MelkhiorVintageComputing/SBusFPGA/sbus-to-ztex-gateware-migen/VexRiscv_FbAccel.v

// Generator : SpinalHDL v1.7.0a    git head : 150a9b9067020722818dfb17df4a23ac712a7af8
// Component : VexRiscv
// Git hash  : 8ab9a9b12e5d8881e3a895b31b6a57d076192df0

`timescale 1ns/1ps

module VexRiscv (
  output reg          iBusWishbone_CYC,
  output reg          iBusWishbone_STB,
  input               iBusWishbone_ACK,
  output              iBusWishbone_WE,
  output     [29:0]   iBusWishbone_ADR,
  input      [31:0]   iBusWishbone_DAT_MISO,
  output     [31:0]   iBusWishbone_DAT_MOSI,
  output     [3:0]    iBusWishbone_SEL,
  input               iBusWishbone_ERR,
  output     [2:0]    iBusWishbone_CTI,
  output     [1:0]    iBusWishbone_BTE,
  output              dBusWishbone_CYC,
  output              dBusWishbone_STB,
  input               dBusWishbone_ACK,
  output              dBusWishbone_WE,
  output     [27:0]   dBusWishbone_ADR,
  input      [127:0]  dBusWishbone_DAT_MISO,
  output     [127:0]  dBusWishbone_DAT_MOSI,
  output     [15:0]   dBusWishbone_SEL,
  input               dBusWishbone_ERR,
  output     [2:0]    dBusWishbone_CTI,
  output     [1:0]    dBusWishbone_BTE,
  input               clk,
  input               reset
);
  localparam ShiftCtrlEnum_DISABLE_1 = 2'd0;
  localparam ShiftCtrlEnum_SLL_1 = 2'd1;
  localparam ShiftCtrlEnum_SRL_1 = 2'd2;
  localparam ShiftCtrlEnum_SRA_1 = 2'd3;
  localparam BranchCtrlEnum_INC = 2'd0;
  localparam BranchCtrlEnum_B = 2'd1;
  localparam BranchCtrlEnum_JAL = 2'd2;
  localparam BranchCtrlEnum_JALR = 2'd3;
  localparam CG6CtrlternaryEnum_CTRL_CMIX = 2'd0;
  localparam CG6CtrlternaryEnum_CTRL_CMOV = 2'd1;
  localparam CG6CtrlternaryEnum_CTRL_FSR = 2'd2;
  localparam CG6CtrlsignextendEnum_CTRL_SEXTdotB = 1'd0;
  localparam CG6CtrlsignextendEnum_CTRL_ZEXTdotH = 1'd1;
  localparam CG6CtrlminmaxEnum_CTRL_MAXU = 1'd0;
  localparam CG6CtrlminmaxEnum_CTRL_MINU = 1'd1;
  localparam CG6CtrlEnum_CTRL_SH2ADD = 3'd0;
  localparam CG6CtrlEnum_CTRL_minmax = 3'd1;
  localparam CG6CtrlEnum_CTRL_signextend = 3'd2;
  localparam CG6CtrlEnum_CTRL_ternary = 3'd3;
  localparam CG6CtrlEnum_CTRL_REV8 = 3'd4;
  localparam AluBitwiseCtrlEnum_XOR_1 = 2'd0;
  localparam AluBitwiseCtrlEnum_OR_1 = 2'd1;
  localparam AluBitwiseCtrlEnum_AND_1 = 2'd2;
  localparam Src3CtrlEnum_RS = 1'd0;
  localparam Src3CtrlEnum_IMI = 1'd1;
  localparam Src2CtrlEnum_RS = 2'd0;
  localparam Src2CtrlEnum_IMI = 2'd1;
  localparam Src2CtrlEnum_IMS = 2'd2;
  localparam Src2CtrlEnum_PC = 2'd3;
  localparam AluCtrlEnum_ADD_SUB = 2'd0;
  localparam AluCtrlEnum_SLT_SLTU = 2'd1;
  localparam AluCtrlEnum_BITWISE = 2'd2;
  localparam Src1CtrlEnum_RS = 2'd0;
  localparam Src1CtrlEnum_IMU = 2'd1;
  localparam Src1CtrlEnum_PC_INCREMENT = 2'd2;
  localparam Src1CtrlEnum_URS1 = 2'd3;

  wire                IBusCachedPlugin_cache_io_flush;
  wire                IBusCachedPlugin_cache_io_cpu_prefetch_isValid;
  wire                IBusCachedPlugin_cache_io_cpu_fetch_isValid;
  wire                IBusCachedPlugin_cache_io_cpu_fetch_isStuck;
  wire                IBusCachedPlugin_cache_io_cpu_fetch_isRemoved;
  wire                IBusCachedPlugin_cache_io_cpu_decode_isValid;
  wire                IBusCachedPlugin_cache_io_cpu_decode_isStuck;
  reg                 IBusCachedPlugin_cache_io_cpu_fill_valid;
  wire                dataCache_1_io_cpu_execute_isValid;
  wire       [31:0]   dataCache_1_io_cpu_execute_address;
  wire       [2:0]    dataCache_1_io_cpu_execute_args_size;
  wire                dataCache_1_io_cpu_memory_isValid;
  wire       [31:0]   dataCache_1_io_cpu_memory_address;
  reg                 dataCache_1_io_cpu_memory_mmuRsp_isIoAccess;
  reg                 dataCache_1_io_cpu_writeBack_isValid;
  reg        [127:0]  dataCache_1_io_cpu_writeBack_storeData;
  wire       [31:0]   dataCache_1_io_cpu_writeBack_address;
  wire                dataCache_1_io_cpu_writeBack_fence_SW;
  wire                dataCache_1_io_cpu_writeBack_fence_SR;
  wire                dataCache_1_io_cpu_writeBack_fence_SO;
  wire                dataCache_1_io_cpu_writeBack_fence_SI;
  wire                dataCache_1_io_cpu_writeBack_fence_PW;
  wire                dataCache_1_io_cpu_writeBack_fence_PR;
  wire                dataCache_1_io_cpu_writeBack_fence_PO;
  wire                dataCache_1_io_cpu_writeBack_fence_PI;
  wire       [3:0]    dataCache_1_io_cpu_writeBack_fence_FM;
  wire                dataCache_1_io_cpu_flush_valid;
  wire                dataCache_1_io_mem_cmd_ready;
  reg        [31:0]   _zz_RegFilePlugin_regFile_port0;
  reg        [31:0]   _zz_RegFilePlugin_regFile_port1;
  reg        [31:0]   _zz_RegFilePlugin_regFile_port2;
  wire                IBusCachedPlugin_cache_io_cpu_prefetch_haltIt;
  wire       [31:0]   IBusCachedPlugin_cache_io_cpu_fetch_data;
  wire       [31:0]   IBusCachedPlugin_cache_io_cpu_fetch_physicalAddress;
  wire                IBusCachedPlugin_cache_io_cpu_decode_error;
  wire                IBusCachedPlugin_cache_io_cpu_decode_mmuRefilling;
  wire                IBusCachedPlugin_cache_io_cpu_decode_mmuException;
  wire       [31:0]   IBusCachedPlugin_cache_io_cpu_decode_data;
  wire                IBusCachedPlugin_cache_io_cpu_decode_cacheMiss;
  wire       [31:0]   IBusCachedPlugin_cache_io_cpu_decode_physicalAddress;
  wire                IBusCachedPlugin_cache_io_mem_cmd_valid;
  wire       [31:0]   IBusCachedPlugin_cache_io_mem_cmd_payload_address;
  wire       [2:0]    IBusCachedPlugin_cache_io_mem_cmd_payload_size;
  wire                dataCache_1_io_cpu_execute_haltIt;
  wire                dataCache_1_io_cpu_execute_refilling;
  wire                dataCache_1_io_cpu_memory_isWrite;
  wire                dataCache_1_io_cpu_writeBack_haltIt;
  wire       [127:0]  dataCache_1_io_cpu_writeBack_data;
  wire                dataCache_1_io_cpu_writeBack_mmuException;
  wire                dataCache_1_io_cpu_writeBack_unalignedAccess;
  wire                dataCache_1_io_cpu_writeBack_accessError;
  wire                dataCache_1_io_cpu_writeBack_isWrite;
  wire                dataCache_1_io_cpu_writeBack_keepMemRspData;
  wire                dataCache_1_io_cpu_writeBack_exclusiveOk;
  wire                dataCache_1_io_cpu_flush_ready;
  wire                dataCache_1_io_cpu_redo;
  wire                dataCache_1_io_mem_cmd_valid;
  wire                dataCache_1_io_mem_cmd_payload_wr;
  wire                dataCache_1_io_mem_cmd_payload_uncached;
  wire       [31:0]   dataCache_1_io_mem_cmd_payload_address;
  wire       [127:0]  dataCache_1_io_mem_cmd_payload_data;
  wire       [15:0]   dataCache_1_io_mem_cmd_payload_mask;
  wire       [2:0]    dataCache_1_io_mem_cmd_payload_size;
  wire                dataCache_1_io_mem_cmd_payload_last;
  wire       [31:0]   _zz_execute_SHIFT_RIGHT;
  wire       [32:0]   _zz_execute_SHIFT_RIGHT_1;
  wire       [32:0]   _zz_execute_SHIFT_RIGHT_2;
  wire       [2:0]    _zz__zz_IBusCachedPlugin_jump_pcLoad_payload_1;
  reg        [31:0]   _zz_IBusCachedPlugin_jump_pcLoad_payload_4;
  wire       [1:0]    _zz_IBusCachedPlugin_jump_pcLoad_payload_5;
  wire       [31:0]   _zz_IBusCachedPlugin_fetchPc_pc;
  wire       [2:0]    _zz_IBusCachedPlugin_fetchPc_pc_1;
  wire       [11:0]   _zz__zz_IBusCachedPlugin_decodePrediction_cmd_hadBranch;
  wire       [31:0]   _zz_IBusCachedPlugin_decodePrediction_cmd_hadBranch_2;
  wire       [19:0]   _zz__zz_2;
  wire       [11:0]   _zz__zz_4;
  wire       [31:0]   _zz__zz_6;
  wire       [31:0]   _zz__zz_6_1;
  wire       [19:0]   _zz__zz_IBusCachedPlugin_predictionJumpInterface_payload;
  wire       [11:0]   _zz__zz_IBusCachedPlugin_predictionJumpInterface_payload_2;
  wire                _zz_IBusCachedPlugin_predictionJumpInterface_payload_4;
  wire                _zz_IBusCachedPlugin_predictionJumpInterface_payload_5;
  wire                _zz_IBusCachedPlugin_predictionJumpInterface_payload_6;
  reg        [7:0]    _zz_writeBack_DBusCachedPlugin_rspShifted;
  wire       [3:0]    _zz_writeBack_DBusCachedPlugin_rspShifted_1;
  reg        [7:0]    _zz_writeBack_DBusCachedPlugin_rspShifted_2;
  wire       [2:0]    _zz_writeBack_DBusCachedPlugin_rspShifted_3;
  reg        [7:0]    _zz_writeBack_DBusCachedPlugin_rspShifted_4;
  wire       [1:0]    _zz_writeBack_DBusCachedPlugin_rspShifted_5;
  reg        [7:0]    _zz_writeBack_DBusCachedPlugin_rspShifted_6;
  wire       [1:0]    _zz_writeBack_DBusCachedPlugin_rspShifted_7;
  reg        [7:0]    _zz_writeBack_DBusCachedPlugin_rspShifted_8;
  wire       [0:0]    _zz_writeBack_DBusCachedPlugin_rspShifted_9;
  reg        [7:0]    _zz_writeBack_DBusCachedPlugin_rspShifted_10;
  wire       [0:0]    _zz_writeBack_DBusCachedPlugin_rspShifted_11;
  reg        [7:0]    _zz_writeBack_DBusCachedPlugin_rspShifted_12;
  wire       [0:0]    _zz_writeBack_DBusCachedPlugin_rspShifted_13;
  reg        [7:0]    _zz_writeBack_DBusCachedPlugin_rspShifted_14;
  wire       [0:0]    _zz_writeBack_DBusCachedPlugin_rspShifted_15;
  wire       [31:0]   _zz__zz_decode_REGFILE_WRITE_VALID_ODD;
  wire       [31:0]   _zz__zz_decode_REGFILE_WRITE_VALID_ODD_1;
  wire       [31:0]   _zz__zz_decode_REGFILE_WRITE_VALID_ODD_2;
  wire       [31:0]   _zz__zz_decode_REGFILE_WRITE_VALID_ODD_3;
  wire                _zz__zz_decode_REGFILE_WRITE_VALID_ODD_4;
  wire       [0:0]    _zz__zz_decode_REGFILE_WRITE_VALID_ODD_5;
  wire                _zz__zz_decode_REGFILE_WRITE_VALID_ODD_6;
  wire       [0:0]    _zz__zz_decode_REGFILE_WRITE_VALID_ODD_7;
  wire       [31:0]   _zz__zz_decode_REGFILE_WRITE_VALID_ODD_8;
  wire       [28:0]   _zz__zz_decode_REGFILE_WRITE_VALID_ODD_9;
  wire       [31:0]   _zz__zz_decode_REGFILE_WRITE_VALID_ODD_10;
  wire       [31:0]   _zz__zz_decode_REGFILE_WRITE_VALID_ODD_11;
  wire                _zz__zz_decode_REGFILE_WRITE_VALID_ODD_12;
  wire       [2:0]    _zz__zz_decode_REGFILE_WRITE_VALID_ODD_13;
  wire       [31:0]   _zz__zz_decode_REGFILE_WRITE_VALID_ODD_14;
  wire       [31:0]   _zz__zz_decode_REGFILE_WRITE_VALID_ODD_15;
  wire       [31:0]   _zz__zz_decode_REGFILE_WRITE_VALID_ODD_16;
  wire       [31:0]   _zz__zz_decode_REGFILE_WRITE_VALID_ODD_17;
  wire                _zz__zz_decode_REGFILE_WRITE_VALID_ODD_18;
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
  wire       [8:0]    _zz__zz_decode_REGFILE_WRITE_VALID_ODD_84;
  wire       [1:0]    _zz__zz_decode_REGFILE_WRITE_VALID_ODD_85;
  wire       [31:0]   _zz__zz_decode_REGFILE_WRITE_VALID_ODD_86;
  wire       [31:0]   _zz__zz_decode_REGFILE_WRITE_VALID_ODD_87;
  wire                _zz__zz_decode_REGFILE_WRITE_VALID_ODD_88;
  wire       [31:0]   _zz__zz_decode_REGFILE_WRITE_VALID_ODD_89;
  wire       [31:0]   _zz__zz_decode_REGFILE_WRITE_VALID_ODD_90;
  wire       [0:0]    _zz__zz_decode_REGFILE_WRITE_VALID_ODD_91;
  wire                _zz__zz_decode_REGFILE_WRITE_VALID_ODD_92;
  wire       [5:0]    _zz__zz_decode_REGFILE_WRITE_VALID_ODD_93;
  wire       [1:0]    _zz__zz_decode_REGFILE_WRITE_VALID_ODD_94;
  wire       [31:0]   _zz__zz_decode_REGFILE_WRITE_VALID_ODD_95;
  wire                _zz__zz_decode_REGFILE_WRITE_VALID_ODD_96;
  wire       [31:0]   _zz__zz_decode_REGFILE_WRITE_VALID_ODD_97;
  wire       [0:0]    _zz__zz_decode_REGFILE_WRITE_VALID_ODD_98;
  wire       [0:0]    _zz__zz_decode_REGFILE_WRITE_VALID_ODD_99;
  wire       [0:0]    _zz__zz_decode_REGFILE_WRITE_VALID_ODD_100;
  wire       [2:0]    _zz__zz_decode_REGFILE_WRITE_VALID_ODD_101;
  wire                _zz__zz_decode_REGFILE_WRITE_VALID_ODD_102;
  wire       [0:0]    _zz__zz_decode_REGFILE_WRITE_VALID_ODD_103;
  wire       [0:0]    _zz__zz_decode_REGFILE_WRITE_VALID_ODD_104;
  wire                _zz_RegFilePlugin_regFile_port;
  wire                _zz_decode_RegFilePlugin_rs1Data;
  wire                _zz_RegFilePlugin_regFile_port_1;
  wire                _zz_decode_RegFilePlugin_rs2Data;
  wire                _zz_RegFilePlugin_regFile_port_2;
  wire                _zz_decode_RegFilePlugin_rs3Data;
  wire       [0:0]    _zz__zz_execute_REGFILE_WRITE_DATA;
  wire       [2:0]    _zz__zz_execute_SRC1;
  wire       [4:0]    _zz__zz_execute_SRC1_1;
  wire       [11:0]   _zz__zz_execute_SRC2_3;
  wire       [31:0]   _zz_execute_SrcPlugin_addSub;
  wire       [31:0]   _zz_execute_SrcPlugin_addSub_1;
  wire       [31:0]   _zz_execute_SrcPlugin_addSub_2;
  wire       [31:0]   _zz_execute_SrcPlugin_addSub_3;
  wire       [31:0]   _zz_execute_SrcPlugin_addSub_4;
  wire       [31:0]   _zz_execute_SrcPlugin_addSub_5;
  wire       [31:0]   _zz_execute_SrcPlugin_addSub_6;
  wire       [31:0]   _zz__zz_execute_CG6Plugin_val_ternary_1;
  wire       [31:0]   _zz_execute_CG6Plugin_val_ternary_3;
  wire       [31:0]   _zz_execute_CG6Plugin_val_ternary_4;
  wire       [31:0]   _zz_execute_CG6Plugin_val_ternary_5;
  wire       [31:0]   _zz__zz_execute_CG6_FINAL_OUTPUT;
  wire       [31:0]   _zz__zz_execute_CG6_FINAL_OUTPUT_1;
  wire       [19:0]   _zz__zz_execute_BranchPlugin_missAlignedTarget_2;
  wire       [11:0]   _zz__zz_execute_BranchPlugin_missAlignedTarget_4;
  wire       [31:0]   _zz__zz_execute_BranchPlugin_missAlignedTarget_6;
  wire       [31:0]   _zz__zz_execute_BranchPlugin_missAlignedTarget_6_1;
  wire       [31:0]   _zz__zz_execute_BranchPlugin_missAlignedTarget_6_2;
  wire       [19:0]   _zz__zz_execute_BranchPlugin_branch_src2_2;
  wire       [11:0]   _zz__zz_execute_BranchPlugin_branch_src2_4;
  wire                _zz_execute_BranchPlugin_branch_src2_6;
  wire                _zz_execute_BranchPlugin_branch_src2_7;
  wire                _zz_execute_BranchPlugin_branch_src2_8;
  wire       [2:0]    _zz_execute_BranchPlugin_branch_src2_9;
  wire       [26:0]   _zz_iBusWishbone_ADR_1;
  wire       [31:0]   execute_BRANCH_CALC;
  wire                execute_BRANCH_DO;
  wire       [31:0]   execute_CG6_FINAL_OUTPUT;
  wire       [31:0]   execute_SHIFT_RIGHT;
  wire       [31:0]   writeBack_REGFILE_WRITE_DATA_ODD;
  wire       [31:0]   memory_REGFILE_WRITE_DATA_ODD;
  wire       [31:0]   execute_REGFILE_WRITE_DATA_ODD;
  wire       [31:0]   execute_REGFILE_WRITE_DATA;
  wire       [31:0]   memory_MEMORY_STORE_DATA_RF;
  wire       [31:0]   execute_MEMORY_STORE_DATA_RF;
  wire                decode_PREDICTION_HAD_BRANCHED2;
  wire                decode_SRC2_FORCE_ZERO;
  wire       [31:0]   execute_RS3;
  wire                decode_REGFILE_WRITE_VALID_ODD;
  wire       [1:0]    _zz_decode_to_execute_BRANCH_CTRL;
  wire       [1:0]    _zz_decode_to_execute_BRANCH_CTRL_1;
  wire       [1:0]    decode_CG6Ctrlternary;
  wire       [1:0]    _zz_decode_CG6Ctrlternary;
  wire       [1:0]    _zz_decode_to_execute_CG6Ctrlternary;
  wire       [1:0]    _zz_decode_to_execute_CG6Ctrlternary_1;
  wire       [0:0]    decode_CG6Ctrlsignextend;
  wire       [0:0]    _zz_decode_CG6Ctrlsignextend;
  wire       [0:0]    _zz_decode_to_execute_CG6Ctrlsignextend;
  wire       [0:0]    _zz_decode_to_execute_CG6Ctrlsignextend_1;
  wire       [0:0]    decode_CG6Ctrlminmax;
  wire       [0:0]    _zz_decode_CG6Ctrlminmax;
  wire       [0:0]    _zz_decode_to_execute_CG6Ctrlminmax;
  wire       [0:0]    _zz_decode_to_execute_CG6Ctrlminmax_1;
  wire       [2:0]    decode_CG6Ctrl;
  wire       [2:0]    _zz_decode_CG6Ctrl;
  wire       [2:0]    _zz_decode_to_execute_CG6Ctrl;
  wire       [2:0]    _zz_decode_to_execute_CG6Ctrl_1;
  wire                execute_IS_CG6;
  wire                decode_IS_CG6;
  wire       [1:0]    _zz_execute_to_memory_SHIFT_CTRL;
  wire       [1:0]    _zz_execute_to_memory_SHIFT_CTRL_1;
  wire       [1:0]    decode_SHIFT_CTRL;
  wire       [1:0]    _zz_decode_SHIFT_CTRL;
  wire       [1:0]    _zz_decode_to_execute_SHIFT_CTRL;
  wire       [1:0]    _zz_decode_to_execute_SHIFT_CTRL_1;
  wire       [1:0]    decode_ALU_BITWISE_CTRL;
  wire       [1:0]    _zz_decode_ALU_BITWISE_CTRL;
  wire       [1:0]    _zz_decode_to_execute_ALU_BITWISE_CTRL;
  wire       [1:0]    _zz_decode_to_execute_ALU_BITWISE_CTRL_1;
  wire                decode_SRC_LESS_UNSIGNED;
  wire       [0:0]    decode_SRC3_CTRL;
  wire       [0:0]    _zz_decode_SRC3_CTRL;
  wire       [0:0]    _zz_decode_to_execute_SRC3_CTRL;
  wire       [0:0]    _zz_decode_to_execute_SRC3_CTRL_1;
  wire                decode_MEMORY_MANAGMENT;
  wire                decode_MEMORY_WR;
  wire                execute_BYPASSABLE_MEMORY_STAGE;
  wire                decode_BYPASSABLE_MEMORY_STAGE;
  wire                decode_BYPASSABLE_EXECUTE_STAGE;
  wire       [1:0]    decode_SRC2_CTRL;
  wire       [1:0]    _zz_decode_SRC2_CTRL;
  wire       [1:0]    _zz_decode_to_execute_SRC2_CTRL;
  wire       [1:0]    _zz_decode_to_execute_SRC2_CTRL_1;
  wire       [1:0]    decode_ALU_CTRL;
  wire       [1:0]    _zz_decode_ALU_CTRL;
  wire       [1:0]    _zz_decode_to_execute_ALU_CTRL;
  wire       [1:0]    _zz_decode_to_execute_ALU_CTRL_1;
  wire       [1:0]    decode_SRC1_CTRL;
  wire       [1:0]    _zz_decode_SRC1_CTRL;
  wire       [1:0]    _zz_decode_to_execute_SRC1_CTRL;
  wire       [1:0]    _zz_decode_to_execute_SRC1_CTRL_1;
  wire                decode_MEMORY_FORCE_CONSTISTENCY;
  wire       [31:0]   writeBack_FORMAL_PC_NEXT;
  wire       [31:0]   memory_FORMAL_PC_NEXT;
  wire       [31:0]   execute_FORMAL_PC_NEXT;
  wire       [31:0]   decode_FORMAL_PC_NEXT;
  wire       [31:0]   memory_PC;
  wire       [31:0]   memory_BRANCH_CALC;
  wire                memory_BRANCH_DO;
  wire       [31:0]   execute_PC;
  wire                execute_PREDICTION_HAD_BRANCHED2;
  wire       [31:0]   execute_RS1;
  wire                execute_BRANCH_COND_RESULT;
  wire       [1:0]    execute_BRANCH_CTRL;
  wire       [1:0]    _zz_execute_BRANCH_CTRL;
  wire                decode_RS3_USE;
  wire                decode_RS2_USE;
  wire                decode_RS1_USE;
  wire       [31:0]   _zz_decode_RS3;
  wire                execute_REGFILE_WRITE_VALID_ODD;
  wire       [31:0]   _zz_decode_RS3_1;
  wire                execute_REGFILE_WRITE_VALID;
  wire                execute_BYPASSABLE_EXECUTE_STAGE;
  wire       [31:0]   _zz_decode_RS3_2;
  wire                memory_REGFILE_WRITE_VALID_ODD;
  wire                memory_REGFILE_WRITE_VALID;
  wire                memory_BYPASSABLE_MEMORY_STAGE;
  wire       [31:0]   memory_INSTRUCTION;
  wire       [31:0]   _zz_decode_RS3_3;
  wire                writeBack_REGFILE_WRITE_VALID_ODD;
  wire                writeBack_REGFILE_WRITE_VALID;
  reg        [31:0]   decode_RS3;
  reg        [31:0]   decode_RS2;
  reg        [31:0]   decode_RS1;
  wire       [31:0]   memory_CG6_FINAL_OUTPUT;
  wire                memory_IS_CG6;
  wire       [2:0]    execute_CG6Ctrl;
  wire       [2:0]    _zz_execute_CG6Ctrl;
  wire       [31:0]   execute_SRC3;
  wire       [1:0]    execute_CG6Ctrlternary;
  wire       [1:0]    _zz_execute_CG6Ctrlternary;
  wire       [0:0]    execute_CG6Ctrlsignextend;
  wire       [0:0]    _zz_execute_CG6Ctrlsignextend;
  wire       [0:0]    execute_CG6Ctrlminmax;
  wire       [0:0]    _zz_execute_CG6Ctrlminmax;
  wire       [31:0]   memory_SHIFT_RIGHT;
  reg        [31:0]   _zz_decode_RS3_4;
  wire       [1:0]    memory_SHIFT_CTRL;
  wire       [1:0]    _zz_memory_SHIFT_CTRL;
  wire       [1:0]    execute_SHIFT_CTRL;
  wire       [1:0]    _zz_execute_SHIFT_CTRL;
  wire                execute_SRC_LESS_UNSIGNED;
  wire                execute_SRC2_FORCE_ZERO;
  wire                execute_SRC_USE_SUB_LESS;
  wire       [0:0]    execute_SRC3_CTRL;
  wire       [0:0]    _zz_execute_SRC3_CTRL;
  wire       [31:0]   _zz_execute_SRC2;
  wire       [1:0]    execute_SRC2_CTRL;
  wire       [1:0]    _zz_execute_SRC2_CTRL;
  wire       [1:0]    execute_SRC1_CTRL;
  wire       [1:0]    _zz_execute_SRC1_CTRL;
  wire                decode_SRC_USE_SUB_LESS;
  wire                decode_SRC_ADD_ZERO;
  wire       [31:0]   execute_SRC_ADD_SUB;
  wire                execute_SRC_LESS;
  wire       [1:0]    execute_ALU_CTRL;
  wire       [1:0]    _zz_execute_ALU_CTRL;
  wire       [31:0]   execute_SRC2;
  wire       [31:0]   execute_SRC1;
  wire       [1:0]    execute_ALU_BITWISE_CTRL;
  wire       [1:0]    _zz_execute_ALU_BITWISE_CTRL;
  wire                _zz_lastStageRegFileWrite_valid;
  reg                 _zz_1;
  wire       [31:0]   _zz_writeBack_RegFilePlugin_rdIndex;
  wire       [31:0]   decode_INSTRUCTION_ANTICIPATED;
  reg                 decode_REGFILE_WRITE_VALID;
  wire       [1:0]    _zz_decode_BRANCH_CTRL;
  wire       [1:0]    _zz_decode_CG6Ctrlternary_1;
  wire       [0:0]    _zz_decode_CG6Ctrlsignextend_1;
  wire       [0:0]    _zz_decode_CG6Ctrlminmax_1;
  wire       [2:0]    _zz_decode_CG6Ctrl_1;
  wire       [1:0]    _zz_decode_SHIFT_CTRL_1;
  wire       [1:0]    _zz_decode_ALU_BITWISE_CTRL_1;
  wire       [0:0]    _zz_decode_SRC3_CTRL_1;
  wire       [1:0]    _zz_decode_SRC2_CTRL_1;
  wire       [1:0]    _zz_decode_ALU_CTRL_1;
  wire       [1:0]    _zz_decode_SRC1_CTRL_1;
  reg        [31:0]   _zz_decode_RS3_5;
  wire       [31:0]   writeBack_MEMORY_STORE_DATA_RF;
  wire       [31:0]   writeBack_REGFILE_WRITE_DATA;
  wire                writeBack_MEMORY_ENABLE;
  wire       [31:0]   memory_REGFILE_WRITE_DATA;
  wire                memory_MEMORY_ENABLE;
  wire                execute_MEMORY_FORCE_CONSTISTENCY;
  wire                execute_MEMORY_MANAGMENT;
  wire       [31:0]   execute_RS2;
  wire                execute_MEMORY_WR;
  wire       [31:0]   execute_SRC_ADD;
  wire                execute_MEMORY_ENABLE;
  wire       [31:0]   execute_INSTRUCTION;
  wire                decode_MEMORY_ENABLE;
  wire                decode_FLUSH_ALL;
  reg                 IBusCachedPlugin_rsp_issueDetected_2;
  reg                 IBusCachedPlugin_rsp_issueDetected_1;
  wire       [1:0]    decode_BRANCH_CTRL;
  wire       [1:0]    _zz_decode_BRANCH_CTRL_1;
  wire       [31:0]   decode_INSTRUCTION;
  reg        [31:0]   _zz_memory_to_writeBack_FORMAL_PC_NEXT;
  reg        [31:0]   _zz_decode_to_execute_FORMAL_PC_NEXT;
  wire       [31:0]   decode_PC;
  wire       [31:0]   writeBack_PC;
  wire       [31:0]   writeBack_INSTRUCTION;
  reg                 decode_arbitration_haltItself;
  reg                 decode_arbitration_haltByOther;
  reg                 decode_arbitration_removeIt;
  wire                decode_arbitration_flushIt;
  reg                 decode_arbitration_flushNext;
  reg                 decode_arbitration_isValid;
  wire                decode_arbitration_isStuck;
  wire                decode_arbitration_isStuckByOthers;
  wire                decode_arbitration_isFlushed;
  wire                decode_arbitration_isMoving;
  wire                decode_arbitration_isFiring;
  reg                 execute_arbitration_haltItself;
  reg                 execute_arbitration_haltByOther;
  reg                 execute_arbitration_removeIt;
  wire                execute_arbitration_flushIt;
  wire                execute_arbitration_flushNext;
  reg                 execute_arbitration_isValid;
  wire                execute_arbitration_isStuck;
  wire                execute_arbitration_isStuckByOthers;
  wire                execute_arbitration_isFlushed;
  wire                execute_arbitration_isMoving;
  wire                execute_arbitration_isFiring;
  wire                memory_arbitration_haltItself;
  wire                memory_arbitration_haltByOther;
  reg                 memory_arbitration_removeIt;
  wire                memory_arbitration_flushIt;
  reg                 memory_arbitration_flushNext;
  reg                 memory_arbitration_isValid;
  wire                memory_arbitration_isStuck;
  wire                memory_arbitration_isStuckByOthers;
  wire                memory_arbitration_isFlushed;
  wire                memory_arbitration_isMoving;
  wire                memory_arbitration_isFiring;
  reg                 writeBack_arbitration_haltItself;
  wire                writeBack_arbitration_haltByOther;
  reg                 writeBack_arbitration_removeIt;
  reg                 writeBack_arbitration_flushIt;
  reg                 writeBack_arbitration_flushNext;
  reg                 writeBack_arbitration_isValid;
  wire                writeBack_arbitration_isStuck;
  wire                writeBack_arbitration_isStuckByOthers;
  wire                writeBack_arbitration_isFlushed;
  wire                writeBack_arbitration_isMoving;
  wire                writeBack_arbitration_isFiring;
  wire       [31:0]   lastStageInstruction /* verilator public */ ;
  wire       [31:0]   lastStagePc /* verilator public */ ;
  wire                lastStageIsValid /* verilator public */ ;
  wire                lastStageIsFiring /* verilator public */ ;
  wire                IBusCachedPlugin_fetcherHalt;
  wire                IBusCachedPlugin_forceNoDecodeCond;
  reg                 IBusCachedPlugin_incomingInstruction;
  wire                IBusCachedPlugin_predictionJumpInterface_valid;
  (* keep , syn_keep *) wire       [31:0]   IBusCachedPlugin_predictionJumpInterface_payload /* synthesis syn_keep = 1 */ ;
  reg                 IBusCachedPlugin_decodePrediction_cmd_hadBranch;
  wire                IBusCachedPlugin_decodePrediction_rsp_wasWrong;
  wire                IBusCachedPlugin_pcValids_0;
  wire                IBusCachedPlugin_pcValids_1;
  wire                IBusCachedPlugin_pcValids_2;
  wire                IBusCachedPlugin_pcValids_3;
  wire                IBusCachedPlugin_mmuBus_cmd_0_isValid;
  wire                IBusCachedPlugin_mmuBus_cmd_0_isStuck;
  wire       [31:0]   IBusCachedPlugin_mmuBus_cmd_0_virtualAddress;
  wire                IBusCachedPlugin_mmuBus_cmd_0_bypassTranslation;
  wire       [31:0]   IBusCachedPlugin_mmuBus_rsp_physicalAddress;
  wire                IBusCachedPlugin_mmuBus_rsp_isIoAccess;
  wire                IBusCachedPlugin_mmuBus_rsp_isPaging;
  wire                IBusCachedPlugin_mmuBus_rsp_allowRead;
  wire                IBusCachedPlugin_mmuBus_rsp_allowWrite;
  wire                IBusCachedPlugin_mmuBus_rsp_allowExecute;
  wire                IBusCachedPlugin_mmuBus_rsp_exception;
  wire                IBusCachedPlugin_mmuBus_rsp_refilling;
  wire                IBusCachedPlugin_mmuBus_rsp_bypassTranslation;
  wire                IBusCachedPlugin_mmuBus_end;
  wire                IBusCachedPlugin_mmuBus_busy;
  wire                dBus_cmd_valid;
  wire                dBus_cmd_ready;
  wire                dBus_cmd_payload_wr;
  wire                dBus_cmd_payload_uncached;
  wire       [31:0]   dBus_cmd_payload_address;
  wire       [127:0]  dBus_cmd_payload_data;
  wire       [15:0]   dBus_cmd_payload_mask;
  wire       [2:0]    dBus_cmd_payload_size;
  wire                dBus_cmd_payload_last;
  wire                dBus_rsp_valid;
  wire       [4:0]    dBus_rsp_payload_aggregated;
  wire                dBus_rsp_payload_last;
  wire       [127:0]  dBus_rsp_payload_data;
  wire                dBus_rsp_payload_error;
  wire                DBusCachedPlugin_mmuBus_cmd_0_isValid;
  wire                DBusCachedPlugin_mmuBus_cmd_0_isStuck;
  wire       [31:0]   DBusCachedPlugin_mmuBus_cmd_0_virtualAddress;
  wire                DBusCachedPlugin_mmuBus_cmd_0_bypassTranslation;
  wire       [31:0]   DBusCachedPlugin_mmuBus_rsp_physicalAddress;
  wire                DBusCachedPlugin_mmuBus_rsp_isIoAccess;
  wire                DBusCachedPlugin_mmuBus_rsp_isPaging;
  wire                DBusCachedPlugin_mmuBus_rsp_allowRead;
  wire                DBusCachedPlugin_mmuBus_rsp_allowWrite;
  wire                DBusCachedPlugin_mmuBus_rsp_allowExecute;
  wire                DBusCachedPlugin_mmuBus_rsp_exception;
  wire                DBusCachedPlugin_mmuBus_rsp_refilling;
  wire                DBusCachedPlugin_mmuBus_rsp_bypassTranslation;
  wire                DBusCachedPlugin_mmuBus_end;
  wire                DBusCachedPlugin_mmuBus_busy;
  reg                 DBusCachedPlugin_redoBranch_valid;
  wire       [31:0]   DBusCachedPlugin_redoBranch_payload;
  wire                BranchPlugin_jumpInterface_valid;
  wire       [31:0]   BranchPlugin_jumpInterface_payload;
  wire                BranchPlugin_inDebugNoFetchFlag;
  wire                IBusCachedPlugin_externalFlush;
  wire                IBusCachedPlugin_jump_pcLoad_valid;
  wire       [31:0]   IBusCachedPlugin_jump_pcLoad_payload;
  wire       [2:0]    _zz_IBusCachedPlugin_jump_pcLoad_payload;
  wire       [2:0]    _zz_IBusCachedPlugin_jump_pcLoad_payload_1;
  wire                _zz_IBusCachedPlugin_jump_pcLoad_payload_2;
  wire                _zz_IBusCachedPlugin_jump_pcLoad_payload_3;
  wire                IBusCachedPlugin_fetchPc_output_valid;
  wire                IBusCachedPlugin_fetchPc_output_ready;
  wire       [31:0]   IBusCachedPlugin_fetchPc_output_payload;
  reg        [31:0]   IBusCachedPlugin_fetchPc_pcReg /* verilator public */ ;
  reg                 IBusCachedPlugin_fetchPc_correction;
  reg                 IBusCachedPlugin_fetchPc_correctionReg;
  wire                IBusCachedPlugin_fetchPc_output_fire;
  wire                IBusCachedPlugin_fetchPc_corrected;
  reg                 IBusCachedPlugin_fetchPc_pcRegPropagate;
  reg                 IBusCachedPlugin_fetchPc_booted;
  reg                 IBusCachedPlugin_fetchPc_inc;
  wire                when_Fetcher_l134;
  wire                IBusCachedPlugin_fetchPc_output_fire_1;
  wire                when_Fetcher_l134_1;
  reg        [31:0]   IBusCachedPlugin_fetchPc_pc;
  wire                IBusCachedPlugin_fetchPc_redo_valid;
  wire       [31:0]   IBusCachedPlugin_fetchPc_redo_payload;
  reg                 IBusCachedPlugin_fetchPc_flushed;
  wire                when_Fetcher_l161;
  reg                 IBusCachedPlugin_iBusRsp_redoFetch;
  wire                IBusCachedPlugin_iBusRsp_stages_0_input_valid;
  wire                IBusCachedPlugin_iBusRsp_stages_0_input_ready;
  wire       [31:0]   IBusCachedPlugin_iBusRsp_stages_0_input_payload;
  wire                IBusCachedPlugin_iBusRsp_stages_0_output_valid;
  wire                IBusCachedPlugin_iBusRsp_stages_0_output_ready;
  wire       [31:0]   IBusCachedPlugin_iBusRsp_stages_0_output_payload;
  reg                 IBusCachedPlugin_iBusRsp_stages_0_halt;
  wire                IBusCachedPlugin_iBusRsp_stages_1_input_valid;
  wire                IBusCachedPlugin_iBusRsp_stages_1_input_ready;
  wire       [31:0]   IBusCachedPlugin_iBusRsp_stages_1_input_payload;
  wire                IBusCachedPlugin_iBusRsp_stages_1_output_valid;
  wire                IBusCachedPlugin_iBusRsp_stages_1_output_ready;
  wire       [31:0]   IBusCachedPlugin_iBusRsp_stages_1_output_payload;
  reg                 IBusCachedPlugin_iBusRsp_stages_1_halt;
  wire                IBusCachedPlugin_iBusRsp_stages_2_input_valid;
  wire                IBusCachedPlugin_iBusRsp_stages_2_input_ready;
  wire       [31:0]   IBusCachedPlugin_iBusRsp_stages_2_input_payload;
  wire                IBusCachedPlugin_iBusRsp_stages_2_output_valid;
  wire                IBusCachedPlugin_iBusRsp_stages_2_output_ready;
  wire       [31:0]   IBusCachedPlugin_iBusRsp_stages_2_output_payload;
  reg                 IBusCachedPlugin_iBusRsp_stages_2_halt;
  wire                _zz_IBusCachedPlugin_iBusRsp_stages_0_input_ready;
  wire                _zz_IBusCachedPlugin_iBusRsp_stages_1_input_ready;
  wire                _zz_IBusCachedPlugin_iBusRsp_stages_2_input_ready;
  wire                IBusCachedPlugin_iBusRsp_flush;
  wire                _zz_IBusCachedPlugin_iBusRsp_stages_0_output_ready;
  wire                _zz_IBusCachedPlugin_iBusRsp_stages_0_output_ready_1;
  reg                 _zz_IBusCachedPlugin_iBusRsp_stages_0_output_ready_2;
  wire                IBusCachedPlugin_iBusRsp_stages_1_output_m2sPipe_valid;
  wire                IBusCachedPlugin_iBusRsp_stages_1_output_m2sPipe_ready;
  wire       [31:0]   IBusCachedPlugin_iBusRsp_stages_1_output_m2sPipe_payload;
  reg                 _zz_IBusCachedPlugin_iBusRsp_stages_1_output_m2sPipe_valid;
  reg        [31:0]   _zz_IBusCachedPlugin_iBusRsp_stages_1_output_m2sPipe_payload;
  reg                 IBusCachedPlugin_iBusRsp_readyForError;
  wire                IBusCachedPlugin_iBusRsp_output_valid;
  wire                IBusCachedPlugin_iBusRsp_output_ready;
  wire       [31:0]   IBusCachedPlugin_iBusRsp_output_payload_pc;
  wire                IBusCachedPlugin_iBusRsp_output_payload_rsp_error;
  wire       [31:0]   IBusCachedPlugin_iBusRsp_output_payload_rsp_inst;
  wire                IBusCachedPlugin_iBusRsp_output_payload_isRvc;
  wire                when_Fetcher_l243;
  wire                when_Fetcher_l323;
  reg                 IBusCachedPlugin_injector_nextPcCalc_valids_0;
  wire                when_Fetcher_l332;
  reg                 IBusCachedPlugin_injector_nextPcCalc_valids_1;
  wire                when_Fetcher_l332_1;
  reg                 IBusCachedPlugin_injector_nextPcCalc_valids_2;
  wire                when_Fetcher_l332_2;
  reg                 IBusCachedPlugin_injector_nextPcCalc_valids_3;
  wire                when_Fetcher_l332_3;
  reg                 IBusCachedPlugin_injector_nextPcCalc_valids_4;
  wire                when_Fetcher_l332_4;
  wire                _zz_IBusCachedPlugin_decodePrediction_cmd_hadBranch;
  reg        [18:0]   _zz_IBusCachedPlugin_decodePrediction_cmd_hadBranch_1;
  wire                _zz_2;
  reg        [10:0]   _zz_3;
  wire                _zz_4;
  reg        [18:0]   _zz_5;
  reg                 _zz_6;
  wire                _zz_IBusCachedPlugin_predictionJumpInterface_payload;
  reg        [10:0]   _zz_IBusCachedPlugin_predictionJumpInterface_payload_1;
  wire                _zz_IBusCachedPlugin_predictionJumpInterface_payload_2;
  reg        [18:0]   _zz_IBusCachedPlugin_predictionJumpInterface_payload_3;
  wire                iBus_cmd_valid;
  wire                iBus_cmd_ready;
  reg        [31:0]   iBus_cmd_payload_address;
  wire       [2:0]    iBus_cmd_payload_size;
  wire                iBus_rsp_valid;
  wire       [31:0]   iBus_rsp_payload_data;
  wire                iBus_rsp_payload_error;
  reg        [31:0]   IBusCachedPlugin_rspCounter;
  wire                IBusCachedPlugin_s0_tightlyCoupledHit;
  reg                 IBusCachedPlugin_s1_tightlyCoupledHit;
  reg                 IBusCachedPlugin_s2_tightlyCoupledHit;
  wire                IBusCachedPlugin_rsp_iBusRspOutputHalt;
  wire                IBusCachedPlugin_rsp_issueDetected;
  reg                 IBusCachedPlugin_rsp_redoFetch;
  wire                when_IBusCachedPlugin_l239;
  wire                when_IBusCachedPlugin_l250;
  wire                when_IBusCachedPlugin_l267;
  wire                dataCache_1_io_mem_cmd_s2mPipe_valid;
  wire                dataCache_1_io_mem_cmd_s2mPipe_ready;
  wire                dataCache_1_io_mem_cmd_s2mPipe_payload_wr;
  wire                dataCache_1_io_mem_cmd_s2mPipe_payload_uncached;
  wire       [31:0]   dataCache_1_io_mem_cmd_s2mPipe_payload_address;
  wire       [127:0]  dataCache_1_io_mem_cmd_s2mPipe_payload_data;
  wire       [15:0]   dataCache_1_io_mem_cmd_s2mPipe_payload_mask;
  wire       [2:0]    dataCache_1_io_mem_cmd_s2mPipe_payload_size;
  wire                dataCache_1_io_mem_cmd_s2mPipe_payload_last;
  reg                 dataCache_1_io_mem_cmd_rValid;
  reg                 dataCache_1_io_mem_cmd_rData_wr;
  reg                 dataCache_1_io_mem_cmd_rData_uncached;
  reg        [31:0]   dataCache_1_io_mem_cmd_rData_address;
  reg        [127:0]  dataCache_1_io_mem_cmd_rData_data;
  reg        [15:0]   dataCache_1_io_mem_cmd_rData_mask;
  reg        [2:0]    dataCache_1_io_mem_cmd_rData_size;
  reg                 dataCache_1_io_mem_cmd_rData_last;
  reg                 dBus_rsp_regNext_valid;
  reg        [4:0]    dBus_rsp_regNext_payload_aggregated;
  reg                 dBus_rsp_regNext_payload_last;
  reg        [127:0]  dBus_rsp_regNext_payload_data;
  reg                 dBus_rsp_regNext_payload_error;
  reg        [31:0]   DBusCachedPlugin_rspCounter;
  wire                when_DBusCachedPlugin_l307;
  wire       [1:0]    execute_DBusCachedPlugin_size;
  reg        [31:0]   _zz_execute_MEMORY_STORE_DATA_RF;
  wire                dataCache_1_io_cpu_flush_isStall;
  wire                when_DBusCachedPlugin_l347;
  wire                when_DBusCachedPlugin_l363;
  wire                when_DBusCachedPlugin_l390;
  wire                when_DBusCachedPlugin_l443;
  wire                when_DBusCachedPlugin_l463;
  wire       [7:0]    writeBack_DBusCachedPlugin_rspSplits_0;
  wire       [7:0]    writeBack_DBusCachedPlugin_rspSplits_1;
  wire       [7:0]    writeBack_DBusCachedPlugin_rspSplits_2;
  wire       [7:0]    writeBack_DBusCachedPlugin_rspSplits_3;
  wire       [7:0]    writeBack_DBusCachedPlugin_rspSplits_4;
  wire       [7:0]    writeBack_DBusCachedPlugin_rspSplits_5;
  wire       [7:0]    writeBack_DBusCachedPlugin_rspSplits_6;
  wire       [7:0]    writeBack_DBusCachedPlugin_rspSplits_7;
  wire       [7:0]    writeBack_DBusCachedPlugin_rspSplits_8;
  wire       [7:0]    writeBack_DBusCachedPlugin_rspSplits_9;
  wire       [7:0]    writeBack_DBusCachedPlugin_rspSplits_10;
  wire       [7:0]    writeBack_DBusCachedPlugin_rspSplits_11;
  wire       [7:0]    writeBack_DBusCachedPlugin_rspSplits_12;
  wire       [7:0]    writeBack_DBusCachedPlugin_rspSplits_13;
  wire       [7:0]    writeBack_DBusCachedPlugin_rspSplits_14;
  wire       [7:0]    writeBack_DBusCachedPlugin_rspSplits_15;
  reg        [127:0]  writeBack_DBusCachedPlugin_rspShifted;
  wire       [31:0]   writeBack_DBusCachedPlugin_rspRf;
  wire       [1:0]    switch_Misc_l211;
  wire                _zz_writeBack_DBusCachedPlugin_rspFormated;
  reg        [31:0]   _zz_writeBack_DBusCachedPlugin_rspFormated_1;
  wire                _zz_writeBack_DBusCachedPlugin_rspFormated_2;
  reg        [31:0]   _zz_writeBack_DBusCachedPlugin_rspFormated_3;
  reg        [31:0]   writeBack_DBusCachedPlugin_rspFormated;
  wire                when_DBusCachedPlugin_l489;
  wire       [35:0]   _zz_decode_REGFILE_WRITE_VALID_ODD;
  wire                _zz_decode_REGFILE_WRITE_VALID_ODD_1;
  wire                _zz_decode_REGFILE_WRITE_VALID_ODD_2;
  wire                _zz_decode_REGFILE_WRITE_VALID_ODD_3;
  wire                _zz_decode_REGFILE_WRITE_VALID_ODD_4;
  wire                _zz_decode_REGFILE_WRITE_VALID_ODD_5;
  wire                _zz_decode_REGFILE_WRITE_VALID_ODD_6;
  wire                _zz_decode_REGFILE_WRITE_VALID_ODD_7;
  wire                _zz_decode_REGFILE_WRITE_VALID_ODD_8;
  wire       [1:0]    _zz_decode_SRC1_CTRL_2;
  wire       [1:0]    _zz_decode_ALU_CTRL_2;
  wire       [1:0]    _zz_decode_SRC2_CTRL_2;
  wire       [0:0]    _zz_decode_SRC3_CTRL_2;
  wire       [1:0]    _zz_decode_ALU_BITWISE_CTRL_2;
  wire       [1:0]    _zz_decode_SHIFT_CTRL_2;
  wire       [2:0]    _zz_decode_CG6Ctrl_2;
  wire       [0:0]    _zz_decode_CG6Ctrlminmax_2;
  wire       [0:0]    _zz_decode_CG6Ctrlsignextend_2;
  wire       [1:0]    _zz_decode_CG6Ctrlternary_2;
  wire       [1:0]    _zz_decode_BRANCH_CTRL_2;
  wire                when_RegFilePlugin_l67;
  wire       [4:0]    decode_RegFilePlugin_regFileReadAddress1;
  wire       [4:0]    decode_RegFilePlugin_regFileReadAddress2;
  wire       [4:0]    decode_RegFilePlugin_regFileReadAddress3;
  wire       [31:0]   decode_RegFilePlugin_rs1Data;
  wire       [31:0]   decode_RegFilePlugin_rs2Data;
  wire       [31:0]   decode_RegFilePlugin_rs3Data;
  wire       [4:0]    writeBack_RegFilePlugin_rdIndex;
  reg                 lastStageRegFileWrite_valid /* verilator public */ ;
  reg        [4:0]    lastStageRegFileWrite_payload_address /* verilator public */ ;
  reg        [31:0]   lastStageRegFileWrite_payload_data /* verilator public */ ;
  reg                 _zz_7;
  reg        [31:0]   execute_IntAluPlugin_bitwise;
  reg        [31:0]   _zz_execute_REGFILE_WRITE_DATA;
  reg        [31:0]   _zz_execute_SRC1;
  wire                _zz_execute_SRC2_1;
  reg        [19:0]   _zz_execute_SRC2_2;
  wire                _zz_execute_SRC2_3;
  reg        [19:0]   _zz_execute_SRC2_4;
  reg        [31:0]   _zz_execute_SRC2_5;
  wire                _zz_execute_SRC3;
  reg        [19:0]   _zz_execute_SRC3_1;
  reg        [31:0]   _zz_execute_SRC3_2;
  reg        [31:0]   execute_SrcPlugin_addSub;
  wire                execute_SrcPlugin_less;
  wire       [4:0]    execute_FullBarrelShifterPlugin_amplitude;
  reg        [31:0]   _zz_execute_FullBarrelShifterPlugin_reversed;
  wire       [31:0]   execute_FullBarrelShifterPlugin_reversed;
  reg        [31:0]   _zz_decode_RS3_6;
  reg        [31:0]   execute_CG6Plugin_val_minmax;
  reg        [31:0]   execute_CG6Plugin_val_signextend;
  wire       [31:0]   _zz_execute_CG6Plugin_val_ternary;
  wire       [31:0]   _zz_execute_CG6Plugin_val_ternary_1;
  wire       [31:0]   _zz_execute_CG6Plugin_val_ternary_2;
  reg        [31:0]   execute_CG6Plugin_val_ternary;
  reg        [31:0]   _zz_execute_CG6_FINAL_OUTPUT;
  wire                when_CG6_l489;
  reg                 HazardSimplePlugin_src0Hazard;
  reg                 HazardSimplePlugin_src1Hazard;
  reg                 HazardSimplePlugin_src2Hazard;
  wire                HazardSimplePlugin_writeBackWrites_valid;
  wire       [4:0]    HazardSimplePlugin_writeBackWrites_payload_address;
  wire       [31:0]   HazardSimplePlugin_writeBackWrites_payload_data;
  wire                HazardSimplePlugin_notAES;
  wire       [4:0]    HazardSimplePlugin_rdIndex;
  wire       [4:0]    HazardSimplePlugin_regFileReadAddress3;
  reg                 HazardSimplePlugin_writeBackBuffer_valid;
  reg        [4:0]    HazardSimplePlugin_writeBackBuffer_payload_address;
  reg        [31:0]   HazardSimplePlugin_writeBackBuffer_payload_data;
  wire                HazardSimplePlugin_addr0Match;
  wire                HazardSimplePlugin_addr1Match;
  wire                HazardSimplePlugin_addr2Match;
  wire                _zz_when_HazardSimplePlugin_l74;
  wire       [4:0]    _zz_when_HazardSimplePlugin_l59;
  wire       [4:0]    _zz_when_HazardSimplePlugin_l74_1;
  wire       [4:0]    _zz_when_HazardSimplePlugin_l65;
  wire                when_HazardSimplePlugin_l58;
  wire                when_HazardSimplePlugin_l59;
  wire                when_HazardSimplePlugin_l62;
  wire                when_HazardSimplePlugin_l65;
  wire                when_HazardSimplePlugin_l74;
  wire                when_HazardSimplePlugin_l77;
  wire                when_HazardSimplePlugin_l80;
  wire                when_HazardSimplePlugin_l56;
  wire                when_HazardSimplePlugin_l71;
  wire                when_HazardSimplePlugin_l86;
  wire                when_HazardSimplePlugin_l87;
  wire                when_HazardSimplePlugin_l88;
  wire                when_HazardSimplePlugin_l91;
  wire                when_HazardSimplePlugin_l94;
  wire                _zz_when_HazardSimplePlugin_l74_2;
  wire       [4:0]    _zz_when_HazardSimplePlugin_l59_1;
  wire       [4:0]    _zz_when_HazardSimplePlugin_l74_3;
  wire       [4:0]    _zz_when_HazardSimplePlugin_l65_1;
  wire                when_HazardSimplePlugin_l59_1;
  wire                when_HazardSimplePlugin_l62_1;
  wire                when_HazardSimplePlugin_l65_1;
  wire                when_HazardSimplePlugin_l74_1;
  wire                when_HazardSimplePlugin_l77_1;
  wire                when_HazardSimplePlugin_l80_1;
  wire                when_HazardSimplePlugin_l56_1;
  wire                when_HazardSimplePlugin_l71_1;
  wire                when_HazardSimplePlugin_l86_1;
  wire                when_HazardSimplePlugin_l87_1;
  wire                when_HazardSimplePlugin_l88_1;
  wire                when_HazardSimplePlugin_l91_1;
  wire                when_HazardSimplePlugin_l94_1;
  wire                _zz_when_HazardSimplePlugin_l74_4;
  wire       [4:0]    _zz_when_HazardSimplePlugin_l59_2;
  wire       [4:0]    _zz_when_HazardSimplePlugin_l74_5;
  wire       [4:0]    _zz_when_HazardSimplePlugin_l65_2;
  wire                when_HazardSimplePlugin_l59_2;
  wire                when_HazardSimplePlugin_l62_2;
  wire                when_HazardSimplePlugin_l65_2;
  wire                when_HazardSimplePlugin_l74_2;
  wire                when_HazardSimplePlugin_l77_2;
  wire                when_HazardSimplePlugin_l80_2;
  wire                when_HazardSimplePlugin_l56_2;
  wire                when_HazardSimplePlugin_l71_2;
  wire                when_HazardSimplePlugin_l86_2;
  wire                when_HazardSimplePlugin_l87_2;
  wire                when_HazardSimplePlugin_l88_2;
  wire                when_HazardSimplePlugin_l91_2;
  wire                when_HazardSimplePlugin_l94_2;
  wire                when_HazardSimplePlugin_l147;
  wire                when_HazardSimplePlugin_l150;
  wire                when_HazardSimplePlugin_l153;
  wire                when_HazardSimplePlugin_l158;
  wire                execute_BranchPlugin_eq;
  wire       [2:0]    switch_Misc_l211_1;
  reg                 _zz_execute_BRANCH_COND_RESULT;
  reg                 _zz_execute_BRANCH_COND_RESULT_1;
  wire                _zz_execute_BranchPlugin_missAlignedTarget;
  reg        [19:0]   _zz_execute_BranchPlugin_missAlignedTarget_1;
  wire                _zz_execute_BranchPlugin_missAlignedTarget_2;
  reg        [10:0]   _zz_execute_BranchPlugin_missAlignedTarget_3;
  wire                _zz_execute_BranchPlugin_missAlignedTarget_4;
  reg        [18:0]   _zz_execute_BranchPlugin_missAlignedTarget_5;
  reg                 _zz_execute_BranchPlugin_missAlignedTarget_6;
  wire                execute_BranchPlugin_missAlignedTarget;
  reg        [31:0]   execute_BranchPlugin_branch_src1;
  reg        [31:0]   execute_BranchPlugin_branch_src2;
  wire                _zz_execute_BranchPlugin_branch_src2;
  reg        [19:0]   _zz_execute_BranchPlugin_branch_src2_1;
  wire                _zz_execute_BranchPlugin_branch_src2_2;
  reg        [10:0]   _zz_execute_BranchPlugin_branch_src2_3;
  wire                _zz_execute_BranchPlugin_branch_src2_4;
  reg        [18:0]   _zz_execute_BranchPlugin_branch_src2_5;
  wire       [31:0]   execute_BranchPlugin_branchAdder;
  wire                when_Pipeline_l124;
  reg        [31:0]   decode_to_execute_PC;
  wire                when_Pipeline_l124_1;
  reg        [31:0]   execute_to_memory_PC;
  wire                when_Pipeline_l124_2;
  reg        [31:0]   memory_to_writeBack_PC;
  wire                when_Pipeline_l124_3;
  reg        [31:0]   decode_to_execute_INSTRUCTION;
  wire                when_Pipeline_l124_4;
  reg        [31:0]   execute_to_memory_INSTRUCTION;
  wire                when_Pipeline_l124_5;
  reg        [31:0]   memory_to_writeBack_INSTRUCTION;
  wire                when_Pipeline_l124_6;
  reg        [31:0]   decode_to_execute_FORMAL_PC_NEXT;
  wire                when_Pipeline_l124_7;
  reg        [31:0]   execute_to_memory_FORMAL_PC_NEXT;
  wire                when_Pipeline_l124_8;
  reg        [31:0]   memory_to_writeBack_FORMAL_PC_NEXT;
  wire                when_Pipeline_l124_9;
  reg                 decode_to_execute_MEMORY_FORCE_CONSTISTENCY;
  wire                when_Pipeline_l124_10;
  reg        [1:0]    decode_to_execute_SRC1_CTRL;
  wire                when_Pipeline_l124_11;
  reg                 decode_to_execute_SRC_USE_SUB_LESS;
  wire                when_Pipeline_l124_12;
  reg                 decode_to_execute_MEMORY_ENABLE;
  wire                when_Pipeline_l124_13;
  reg                 execute_to_memory_MEMORY_ENABLE;
  wire                when_Pipeline_l124_14;
  reg                 memory_to_writeBack_MEMORY_ENABLE;
  wire                when_Pipeline_l124_15;
  reg        [1:0]    decode_to_execute_ALU_CTRL;
  wire                when_Pipeline_l124_16;
  reg        [1:0]    decode_to_execute_SRC2_CTRL;
  wire                when_Pipeline_l124_17;
  reg                 decode_to_execute_REGFILE_WRITE_VALID;
  wire                when_Pipeline_l124_18;
  reg                 execute_to_memory_REGFILE_WRITE_VALID;
  wire                when_Pipeline_l124_19;
  reg                 memory_to_writeBack_REGFILE_WRITE_VALID;
  wire                when_Pipeline_l124_20;
  reg                 decode_to_execute_BYPASSABLE_EXECUTE_STAGE;
  wire                when_Pipeline_l124_21;
  reg                 decode_to_execute_BYPASSABLE_MEMORY_STAGE;
  wire                when_Pipeline_l124_22;
  reg                 execute_to_memory_BYPASSABLE_MEMORY_STAGE;
  wire                when_Pipeline_l124_23;
  reg                 decode_to_execute_MEMORY_WR;
  wire                when_Pipeline_l124_24;
  reg                 decode_to_execute_MEMORY_MANAGMENT;
  wire                when_Pipeline_l124_25;
  reg        [0:0]    decode_to_execute_SRC3_CTRL;
  wire                when_Pipeline_l124_26;
  reg                 decode_to_execute_SRC_LESS_UNSIGNED;
  wire                when_Pipeline_l124_27;
  reg        [1:0]    decode_to_execute_ALU_BITWISE_CTRL;
  wire                when_Pipeline_l124_28;
  reg        [1:0]    decode_to_execute_SHIFT_CTRL;
  wire                when_Pipeline_l124_29;
  reg        [1:0]    execute_to_memory_SHIFT_CTRL;
  wire                when_Pipeline_l124_30;
  reg                 decode_to_execute_IS_CG6;
  wire                when_Pipeline_l124_31;
  reg                 execute_to_memory_IS_CG6;
  wire                when_Pipeline_l124_32;
  reg        [2:0]    decode_to_execute_CG6Ctrl;
  wire                when_Pipeline_l124_33;
  reg        [0:0]    decode_to_execute_CG6Ctrlminmax;
  wire                when_Pipeline_l124_34;
  reg        [0:0]    decode_to_execute_CG6Ctrlsignextend;
  wire                when_Pipeline_l124_35;
  reg        [1:0]    decode_to_execute_CG6Ctrlternary;
  wire                when_Pipeline_l124_36;
  reg        [1:0]    decode_to_execute_BRANCH_CTRL;
  wire                when_Pipeline_l124_37;
  reg                 decode_to_execute_REGFILE_WRITE_VALID_ODD;
  wire                when_Pipeline_l124_38;
  reg                 execute_to_memory_REGFILE_WRITE_VALID_ODD;
  wire                when_Pipeline_l124_39;
  reg                 memory_to_writeBack_REGFILE_WRITE_VALID_ODD;
  wire                when_Pipeline_l124_40;
  reg        [31:0]   decode_to_execute_RS1;
  wire                when_Pipeline_l124_41;
  reg        [31:0]   decode_to_execute_RS2;
  wire                when_Pipeline_l124_42;
  reg        [31:0]   decode_to_execute_RS3;
  wire                when_Pipeline_l124_43;
  reg                 decode_to_execute_SRC2_FORCE_ZERO;
  wire                when_Pipeline_l124_44;
  reg                 decode_to_execute_PREDICTION_HAD_BRANCHED2;
  wire                when_Pipeline_l124_45;
  reg        [31:0]   execute_to_memory_MEMORY_STORE_DATA_RF;
  wire                when_Pipeline_l124_46;
  reg        [31:0]   memory_to_writeBack_MEMORY_STORE_DATA_RF;
  wire                when_Pipeline_l124_47;
  reg        [31:0]   execute_to_memory_REGFILE_WRITE_DATA;
  wire                when_Pipeline_l124_48;
  reg        [31:0]   memory_to_writeBack_REGFILE_WRITE_DATA;
  wire                when_Pipeline_l124_49;
  reg        [31:0]   execute_to_memory_REGFILE_WRITE_DATA_ODD;
  wire                when_Pipeline_l124_50;
  reg        [31:0]   memory_to_writeBack_REGFILE_WRITE_DATA_ODD;
  wire                when_Pipeline_l124_51;
  reg        [31:0]   execute_to_memory_SHIFT_RIGHT;
  wire                when_Pipeline_l124_52;
  reg        [31:0]   execute_to_memory_CG6_FINAL_OUTPUT;
  wire                when_Pipeline_l124_53;
  reg                 execute_to_memory_BRANCH_DO;
  wire                when_Pipeline_l124_54;
  reg        [31:0]   execute_to_memory_BRANCH_CALC;
  wire                when_Pipeline_l151;
  wire                when_Pipeline_l154;
  wire                when_Pipeline_l151_1;
  wire                when_Pipeline_l154_1;
  wire                when_Pipeline_l151_2;
  wire                when_Pipeline_l154_2;
  reg        [2:0]    _zz_iBusWishbone_ADR;
  wire                when_InstructionCache_l239;
  reg                 _zz_iBus_rsp_valid;
  reg        [31:0]   iBusWishbone_DAT_MISO_regNext;
  reg        [0:0]    _zz_dBus_cmd_ready;
  wire                _zz_dBus_cmd_ready_1;
  wire                _zz_dBus_cmd_ready_2;
  wire                _zz_dBus_cmd_ready_3;
  wire                _zz_dBus_cmd_ready_4;
  wire                _zz_dBus_cmd_ready_5;
  reg                 _zz_dBus_rsp_valid;
  reg        [127:0]  dBusWishbone_DAT_MISO_regNext;
  `ifndef SYNTHESIS
  reg [31:0] _zz_decode_to_execute_BRANCH_CTRL_string;
  reg [31:0] _zz_decode_to_execute_BRANCH_CTRL_1_string;
  reg [71:0] decode_CG6Ctrlternary_string;
  reg [71:0] _zz_decode_CG6Ctrlternary_string;
  reg [71:0] _zz_decode_to_execute_CG6Ctrlternary_string;
  reg [71:0] _zz_decode_to_execute_CG6Ctrlternary_1_string;
  reg [103:0] decode_CG6Ctrlsignextend_string;
  reg [103:0] _zz_decode_CG6Ctrlsignextend_string;
  reg [103:0] _zz_decode_to_execute_CG6Ctrlsignextend_string;
  reg [103:0] _zz_decode_to_execute_CG6Ctrlsignextend_1_string;
  reg [71:0] decode_CG6Ctrlminmax_string;
  reg [71:0] _zz_decode_CG6Ctrlminmax_string;
  reg [71:0] _zz_decode_to_execute_CG6Ctrlminmax_string;
  reg [71:0] _zz_decode_to_execute_CG6Ctrlminmax_1_string;
  reg [119:0] decode_CG6Ctrl_string;
  reg [119:0] _zz_decode_CG6Ctrl_string;
  reg [119:0] _zz_decode_to_execute_CG6Ctrl_string;
  reg [119:0] _zz_decode_to_execute_CG6Ctrl_1_string;
  reg [71:0] _zz_execute_to_memory_SHIFT_CTRL_string;
  reg [71:0] _zz_execute_to_memory_SHIFT_CTRL_1_string;
  reg [71:0] decode_SHIFT_CTRL_string;
  reg [71:0] _zz_decode_SHIFT_CTRL_string;
  reg [71:0] _zz_decode_to_execute_SHIFT_CTRL_string;
  reg [71:0] _zz_decode_to_execute_SHIFT_CTRL_1_string;
  reg [39:0] decode_ALU_BITWISE_CTRL_string;
  reg [39:0] _zz_decode_ALU_BITWISE_CTRL_string;
  reg [39:0] _zz_decode_to_execute_ALU_BITWISE_CTRL_string;
  reg [39:0] _zz_decode_to_execute_ALU_BITWISE_CTRL_1_string;
  reg [23:0] decode_SRC3_CTRL_string;
  reg [23:0] _zz_decode_SRC3_CTRL_string;
  reg [23:0] _zz_decode_to_execute_SRC3_CTRL_string;
  reg [23:0] _zz_decode_to_execute_SRC3_CTRL_1_string;
  reg [23:0] decode_SRC2_CTRL_string;
  reg [23:0] _zz_decode_SRC2_CTRL_string;
  reg [23:0] _zz_decode_to_execute_SRC2_CTRL_string;
  reg [23:0] _zz_decode_to_execute_SRC2_CTRL_1_string;
  reg [63:0] decode_ALU_CTRL_string;
  reg [63:0] _zz_decode_ALU_CTRL_string;
  reg [63:0] _zz_decode_to_execute_ALU_CTRL_string;
  reg [63:0] _zz_decode_to_execute_ALU_CTRL_1_string;
  reg [95:0] decode_SRC1_CTRL_string;
  reg [95:0] _zz_decode_SRC1_CTRL_string;
  reg [95:0] _zz_decode_to_execute_SRC1_CTRL_string;
  reg [95:0] _zz_decode_to_execute_SRC1_CTRL_1_string;
  reg [31:0] execute_BRANCH_CTRL_string;
  reg [31:0] _zz_execute_BRANCH_CTRL_string;
  reg [119:0] execute_CG6Ctrl_string;
  reg [119:0] _zz_execute_CG6Ctrl_string;
  reg [71:0] execute_CG6Ctrlternary_string;
  reg [71:0] _zz_execute_CG6Ctrlternary_string;
  reg [103:0] execute_CG6Ctrlsignextend_string;
  reg [103:0] _zz_execute_CG6Ctrlsignextend_string;
  reg [71:0] execute_CG6Ctrlminmax_string;
  reg [71:0] _zz_execute_CG6Ctrlminmax_string;
  reg [71:0] memory_SHIFT_CTRL_string;
  reg [71:0] _zz_memory_SHIFT_CTRL_string;
  reg [71:0] execute_SHIFT_CTRL_string;
  reg [71:0] _zz_execute_SHIFT_CTRL_string;
  reg [23:0] execute_SRC3_CTRL_string;
  reg [23:0] _zz_execute_SRC3_CTRL_string;
  reg [23:0] execute_SRC2_CTRL_string;
  reg [23:0] _zz_execute_SRC2_CTRL_string;
  reg [95:0] execute_SRC1_CTRL_string;
  reg [95:0] _zz_execute_SRC1_CTRL_string;
  reg [63:0] execute_ALU_CTRL_string;
  reg [63:0] _zz_execute_ALU_CTRL_string;
  reg [39:0] execute_ALU_BITWISE_CTRL_string;
  reg [39:0] _zz_execute_ALU_BITWISE_CTRL_string;
  reg [31:0] _zz_decode_BRANCH_CTRL_string;
  reg [71:0] _zz_decode_CG6Ctrlternary_1_string;
  reg [103:0] _zz_decode_CG6Ctrlsignextend_1_string;
  reg [71:0] _zz_decode_CG6Ctrlminmax_1_string;
  reg [119:0] _zz_decode_CG6Ctrl_1_string;
  reg [71:0] _zz_decode_SHIFT_CTRL_1_string;
  reg [39:0] _zz_decode_ALU_BITWISE_CTRL_1_string;
  reg [23:0] _zz_decode_SRC3_CTRL_1_string;
  reg [23:0] _zz_decode_SRC2_CTRL_1_string;
  reg [63:0] _zz_decode_ALU_CTRL_1_string;
  reg [95:0] _zz_decode_SRC1_CTRL_1_string;
  reg [31:0] decode_BRANCH_CTRL_string;
  reg [31:0] _zz_decode_BRANCH_CTRL_1_string;
  reg [95:0] _zz_decode_SRC1_CTRL_2_string;
  reg [63:0] _zz_decode_ALU_CTRL_2_string;
  reg [23:0] _zz_decode_SRC2_CTRL_2_string;
  reg [23:0] _zz_decode_SRC3_CTRL_2_string;
  reg [39:0] _zz_decode_ALU_BITWISE_CTRL_2_string;
  reg [71:0] _zz_decode_SHIFT_CTRL_2_string;
  reg [119:0] _zz_decode_CG6Ctrl_2_string;
  reg [71:0] _zz_decode_CG6Ctrlminmax_2_string;
  reg [103:0] _zz_decode_CG6Ctrlsignextend_2_string;
  reg [71:0] _zz_decode_CG6Ctrlternary_2_string;
  reg [31:0] _zz_decode_BRANCH_CTRL_2_string;
  reg [95:0] decode_to_execute_SRC1_CTRL_string;
  reg [63:0] decode_to_execute_ALU_CTRL_string;
  reg [23:0] decode_to_execute_SRC2_CTRL_string;
  reg [23:0] decode_to_execute_SRC3_CTRL_string;
  reg [39:0] decode_to_execute_ALU_BITWISE_CTRL_string;
  reg [71:0] decode_to_execute_SHIFT_CTRL_string;
  reg [71:0] execute_to_memory_SHIFT_CTRL_string;
  reg [119:0] decode_to_execute_CG6Ctrl_string;
  reg [71:0] decode_to_execute_CG6Ctrlminmax_string;
  reg [103:0] decode_to_execute_CG6Ctrlsignextend_string;
  reg [71:0] decode_to_execute_CG6Ctrlternary_string;
  reg [31:0] decode_to_execute_BRANCH_CTRL_string;
  `endif

  reg [31:0] RegFilePlugin_regFile [0:31] /* verilator public */ ;

  assign _zz_execute_SHIFT_RIGHT_1 = ($signed(_zz_execute_SHIFT_RIGHT_2) >>> execute_FullBarrelShifterPlugin_amplitude);
  assign _zz_execute_SHIFT_RIGHT = _zz_execute_SHIFT_RIGHT_1[31 : 0];
  assign _zz_execute_SHIFT_RIGHT_2 = {((execute_SHIFT_CTRL == ShiftCtrlEnum_SRA_1) && execute_FullBarrelShifterPlugin_reversed[31]),execute_FullBarrelShifterPlugin_reversed};
  assign _zz__zz_IBusCachedPlugin_jump_pcLoad_payload_1 = (_zz_IBusCachedPlugin_jump_pcLoad_payload - 3'b001);
  assign _zz_IBusCachedPlugin_fetchPc_pc_1 = {IBusCachedPlugin_fetchPc_inc,2'b00};
  assign _zz_IBusCachedPlugin_fetchPc_pc = {29'd0, _zz_IBusCachedPlugin_fetchPc_pc_1};
  assign _zz__zz_IBusCachedPlugin_decodePrediction_cmd_hadBranch = {{{decode_INSTRUCTION[31],decode_INSTRUCTION[7]},decode_INSTRUCTION[30 : 25]},decode_INSTRUCTION[11 : 8]};
  assign _zz_IBusCachedPlugin_decodePrediction_cmd_hadBranch_2 = {{_zz_IBusCachedPlugin_decodePrediction_cmd_hadBranch_1,{{{decode_INSTRUCTION[31],decode_INSTRUCTION[7]},decode_INSTRUCTION[30 : 25]},decode_INSTRUCTION[11 : 8]}},1'b0};
  assign _zz__zz_2 = {{{decode_INSTRUCTION[31],decode_INSTRUCTION[19 : 12]},decode_INSTRUCTION[20]},decode_INSTRUCTION[30 : 21]};
  assign _zz__zz_4 = {{{decode_INSTRUCTION[31],decode_INSTRUCTION[7]},decode_INSTRUCTION[30 : 25]},decode_INSTRUCTION[11 : 8]};
  assign _zz__zz_6 = {{_zz_3,{{{decode_INSTRUCTION[31],decode_INSTRUCTION[19 : 12]},decode_INSTRUCTION[20]},decode_INSTRUCTION[30 : 21]}},1'b0};
  assign _zz__zz_6_1 = {{_zz_5,{{{decode_INSTRUCTION[31],decode_INSTRUCTION[7]},decode_INSTRUCTION[30 : 25]},decode_INSTRUCTION[11 : 8]}},1'b0};
  assign _zz__zz_IBusCachedPlugin_predictionJumpInterface_payload = {{{decode_INSTRUCTION[31],decode_INSTRUCTION[19 : 12]},decode_INSTRUCTION[20]},decode_INSTRUCTION[30 : 21]};
  assign _zz__zz_IBusCachedPlugin_predictionJumpInterface_payload_2 = {{{decode_INSTRUCTION[31],decode_INSTRUCTION[7]},decode_INSTRUCTION[30 : 25]},decode_INSTRUCTION[11 : 8]};
  assign _zz__zz_execute_REGFILE_WRITE_DATA = execute_SRC_LESS;
  assign _zz__zz_execute_SRC1 = 3'b100;
  assign _zz__zz_execute_SRC1_1 = execute_INSTRUCTION[19 : 15];
  assign _zz__zz_execute_SRC2_3 = {execute_INSTRUCTION[31 : 25],execute_INSTRUCTION[11 : 7]};
  assign _zz_execute_SrcPlugin_addSub = ($signed(_zz_execute_SrcPlugin_addSub_1) + $signed(_zz_execute_SrcPlugin_addSub_4));
  assign _zz_execute_SrcPlugin_addSub_1 = ($signed(_zz_execute_SrcPlugin_addSub_2) + $signed(_zz_execute_SrcPlugin_addSub_3));
  assign _zz_execute_SrcPlugin_addSub_2 = execute_SRC1;
  assign _zz_execute_SrcPlugin_addSub_3 = (execute_SRC_USE_SUB_LESS ? (~ execute_SRC2) : execute_SRC2);
  assign _zz_execute_SrcPlugin_addSub_4 = (execute_SRC_USE_SUB_LESS ? _zz_execute_SrcPlugin_addSub_5 : _zz_execute_SrcPlugin_addSub_6);
  assign _zz_execute_SrcPlugin_addSub_5 = 32'h00000001;
  assign _zz_execute_SrcPlugin_addSub_6 = 32'h0;
  assign _zz__zz_execute_CG6Plugin_val_ternary_1 = (_zz_execute_CG6Plugin_val_ternary - 32'h00000020);
  assign _zz_execute_CG6Plugin_val_ternary_3 = (_zz_execute_CG6Plugin_val_ternary_2 >>> _zz_execute_CG6Plugin_val_ternary_1);
  assign _zz_execute_CG6Plugin_val_ternary_4 = (((_zz_execute_CG6Plugin_val_ternary_1 == _zz_execute_CG6Plugin_val_ternary) ? execute_SRC3 : execute_SRC1) <<< _zz_execute_CG6Plugin_val_ternary_5);
  assign _zz_execute_CG6Plugin_val_ternary_5 = (32'h00000020 - _zz_execute_CG6Plugin_val_ternary_1);
  assign _zz__zz_execute_CG6_FINAL_OUTPUT = (_zz__zz_execute_CG6_FINAL_OUTPUT_1 + execute_SRC2);
  assign _zz__zz_execute_CG6_FINAL_OUTPUT_1 = (execute_SRC1 <<< 2);
  assign _zz__zz_execute_BranchPlugin_missAlignedTarget_2 = {{{execute_INSTRUCTION[31],execute_INSTRUCTION[19 : 12]},execute_INSTRUCTION[20]},execute_INSTRUCTION[30 : 21]};
  assign _zz__zz_execute_BranchPlugin_missAlignedTarget_4 = {{{execute_INSTRUCTION[31],execute_INSTRUCTION[7]},execute_INSTRUCTION[30 : 25]},execute_INSTRUCTION[11 : 8]};
  assign _zz__zz_execute_BranchPlugin_missAlignedTarget_6 = {_zz_execute_BranchPlugin_missAlignedTarget_1,execute_INSTRUCTION[31 : 20]};
  assign _zz__zz_execute_BranchPlugin_missAlignedTarget_6_1 = {{_zz_execute_BranchPlugin_missAlignedTarget_3,{{{execute_INSTRUCTION[31],execute_INSTRUCTION[19 : 12]},execute_INSTRUCTION[20]},execute_INSTRUCTION[30 : 21]}},1'b0};
  assign _zz__zz_execute_BranchPlugin_missAlignedTarget_6_2 = {{_zz_execute_BranchPlugin_missAlignedTarget_5,{{{execute_INSTRUCTION[31],execute_INSTRUCTION[7]},execute_INSTRUCTION[30 : 25]},execute_INSTRUCTION[11 : 8]}},1'b0};
  assign _zz__zz_execute_BranchPlugin_branch_src2_2 = {{{execute_INSTRUCTION[31],execute_INSTRUCTION[19 : 12]},execute_INSTRUCTION[20]},execute_INSTRUCTION[30 : 21]};
  assign _zz__zz_execute_BranchPlugin_branch_src2_4 = {{{execute_INSTRUCTION[31],execute_INSTRUCTION[7]},execute_INSTRUCTION[30 : 25]},execute_INSTRUCTION[11 : 8]};
  assign _zz_execute_BranchPlugin_branch_src2_9 = 3'b100;
  assign _zz_iBusWishbone_ADR_1 = (iBus_cmd_payload_address >>> 5);
  assign _zz_decode_RegFilePlugin_rs1Data = 1'b1;
  assign _zz_decode_RegFilePlugin_rs2Data = 1'b1;
  assign _zz_decode_RegFilePlugin_rs3Data = 1'b1;
  assign _zz_IBusCachedPlugin_jump_pcLoad_payload_5 = {_zz_IBusCachedPlugin_jump_pcLoad_payload_3,_zz_IBusCachedPlugin_jump_pcLoad_payload_2};
  assign _zz_writeBack_DBusCachedPlugin_rspShifted_1 = dataCache_1_io_cpu_writeBack_address[3 : 0];
  assign _zz_writeBack_DBusCachedPlugin_rspShifted_3 = dataCache_1_io_cpu_writeBack_address[3 : 1];
  assign _zz_writeBack_DBusCachedPlugin_rspShifted_5 = dataCache_1_io_cpu_writeBack_address[3 : 2];
  assign _zz_writeBack_DBusCachedPlugin_rspShifted_7 = dataCache_1_io_cpu_writeBack_address[3 : 2];
  assign _zz_writeBack_DBusCachedPlugin_rspShifted_9 = dataCache_1_io_cpu_writeBack_address[3 : 3];
  assign _zz_writeBack_DBusCachedPlugin_rspShifted_11 = dataCache_1_io_cpu_writeBack_address[3 : 3];
  assign _zz_writeBack_DBusCachedPlugin_rspShifted_13 = dataCache_1_io_cpu_writeBack_address[3 : 3];
  assign _zz_writeBack_DBusCachedPlugin_rspShifted_15 = dataCache_1_io_cpu_writeBack_address[3 : 3];
  assign _zz_IBusCachedPlugin_predictionJumpInterface_payload_4 = decode_INSTRUCTION[31];
  assign _zz_IBusCachedPlugin_predictionJumpInterface_payload_5 = decode_INSTRUCTION[31];
  assign _zz_IBusCachedPlugin_predictionJumpInterface_payload_6 = decode_INSTRUCTION[7];
  assign _zz__zz_decode_REGFILE_WRITE_VALID_ODD = (decode_INSTRUCTION & 32'h0000001c);
  assign _zz__zz_decode_REGFILE_WRITE_VALID_ODD_1 = 32'h00000004;
  assign _zz__zz_decode_REGFILE_WRITE_VALID_ODD_2 = (decode_INSTRUCTION & 32'h00000048);
  assign _zz__zz_decode_REGFILE_WRITE_VALID_ODD_3 = 32'h00000040;
  assign _zz__zz_decode_REGFILE_WRITE_VALID_ODD_4 = ((decode_INSTRUCTION & 32'h02000000) == 32'h0);
  assign _zz__zz_decode_REGFILE_WRITE_VALID_ODD_5 = ((decode_INSTRUCTION & 32'h02004000) == 32'h02004000);
  assign _zz__zz_decode_REGFILE_WRITE_VALID_ODD_6 = (|_zz_decode_REGFILE_WRITE_VALID_ODD_7);
  assign _zz__zz_decode_REGFILE_WRITE_VALID_ODD_7 = (|((decode_INSTRUCTION & _zz__zz_decode_REGFILE_WRITE_VALID_ODD_8) == 32'h0));
  assign _zz__zz_decode_REGFILE_WRITE_VALID_ODD_9 = {(|(_zz__zz_decode_REGFILE_WRITE_VALID_ODD_10 == _zz__zz_decode_REGFILE_WRITE_VALID_ODD_11)),{(|_zz__zz_decode_REGFILE_WRITE_VALID_ODD_12),{(|_zz__zz_decode_REGFILE_WRITE_VALID_ODD_13),{_zz__zz_decode_REGFILE_WRITE_VALID_ODD_18,{_zz__zz_decode_REGFILE_WRITE_VALID_ODD_21,_zz__zz_decode_REGFILE_WRITE_VALID_ODD_29}}}}};
  assign _zz__zz_decode_REGFILE_WRITE_VALID_ODD_8 = 32'h40000000;
  assign _zz__zz_decode_REGFILE_WRITE_VALID_ODD_10 = (decode_INSTRUCTION & 32'h00002000);
  assign _zz__zz_decode_REGFILE_WRITE_VALID_ODD_11 = 32'h0;
  assign _zz__zz_decode_REGFILE_WRITE_VALID_ODD_12 = ((decode_INSTRUCTION & 32'h00400020) == 32'h0);
  assign _zz__zz_decode_REGFILE_WRITE_VALID_ODD_13 = {_zz_decode_REGFILE_WRITE_VALID_ODD_8,{(_zz__zz_decode_REGFILE_WRITE_VALID_ODD_14 == _zz__zz_decode_REGFILE_WRITE_VALID_ODD_15),(_zz__zz_decode_REGFILE_WRITE_VALID_ODD_16 == _zz__zz_decode_REGFILE_WRITE_VALID_ODD_17)}};
  assign _zz__zz_decode_REGFILE_WRITE_VALID_ODD_18 = (|{(_zz__zz_decode_REGFILE_WRITE_VALID_ODD_19 == _zz__zz_decode_REGFILE_WRITE_VALID_ODD_20),_zz_decode_REGFILE_WRITE_VALID_ODD_8});
  assign _zz__zz_decode_REGFILE_WRITE_VALID_ODD_21 = (|{_zz__zz_decode_REGFILE_WRITE_VALID_ODD_22,{_zz__zz_decode_REGFILE_WRITE_VALID_ODD_23,_zz__zz_decode_REGFILE_WRITE_VALID_ODD_24}});
  assign _zz__zz_decode_REGFILE_WRITE_VALID_ODD_29 = {(|_zz__zz_decode_REGFILE_WRITE_VALID_ODD_30),{(|_zz__zz_decode_REGFILE_WRITE_VALID_ODD_31),{_zz__zz_decode_REGFILE_WRITE_VALID_ODD_36,{_zz__zz_decode_REGFILE_WRITE_VALID_ODD_39,_zz__zz_decode_REGFILE_WRITE_VALID_ODD_41}}}};
  assign _zz__zz_decode_REGFILE_WRITE_VALID_ODD_14 = (decode_INSTRUCTION & 32'h00004000);
  assign _zz__zz_decode_REGFILE_WRITE_VALID_ODD_15 = 32'h0;
  assign _zz__zz_decode_REGFILE_WRITE_VALID_ODD_16 = (decode_INSTRUCTION & 32'h22000000);
  assign _zz__zz_decode_REGFILE_WRITE_VALID_ODD_17 = 32'h0;
  assign _zz__zz_decode_REGFILE_WRITE_VALID_ODD_19 = (decode_INSTRUCTION & 32'h02000000);
  assign _zz__zz_decode_REGFILE_WRITE_VALID_ODD_20 = 32'h02000000;
  assign _zz__zz_decode_REGFILE_WRITE_VALID_ODD_22 = ((decode_INSTRUCTION & 32'h08004064) == 32'h08004020);
  assign _zz__zz_decode_REGFILE_WRITE_VALID_ODD_23 = _zz_decode_REGFILE_WRITE_VALID_ODD_7;
  assign _zz__zz_decode_REGFILE_WRITE_VALID_ODD_24 = {(_zz__zz_decode_REGFILE_WRITE_VALID_ODD_25 == _zz__zz_decode_REGFILE_WRITE_VALID_ODD_26),(_zz__zz_decode_REGFILE_WRITE_VALID_ODD_27 == _zz__zz_decode_REGFILE_WRITE_VALID_ODD_28)};
  assign _zz__zz_decode_REGFILE_WRITE_VALID_ODD_30 = ((decode_INSTRUCTION & 32'h0c007014) == 32'h00005010);
  assign _zz__zz_decode_REGFILE_WRITE_VALID_ODD_31 = {(_zz__zz_decode_REGFILE_WRITE_VALID_ODD_32 == _zz__zz_decode_REGFILE_WRITE_VALID_ODD_33),(_zz__zz_decode_REGFILE_WRITE_VALID_ODD_34 == _zz__zz_decode_REGFILE_WRITE_VALID_ODD_35)};
  assign _zz__zz_decode_REGFILE_WRITE_VALID_ODD_36 = (|(_zz__zz_decode_REGFILE_WRITE_VALID_ODD_37 == _zz__zz_decode_REGFILE_WRITE_VALID_ODD_38));
  assign _zz__zz_decode_REGFILE_WRITE_VALID_ODD_39 = (|_zz__zz_decode_REGFILE_WRITE_VALID_ODD_40);
  assign _zz__zz_decode_REGFILE_WRITE_VALID_ODD_41 = {(|_zz__zz_decode_REGFILE_WRITE_VALID_ODD_42),{_zz__zz_decode_REGFILE_WRITE_VALID_ODD_43,{_zz__zz_decode_REGFILE_WRITE_VALID_ODD_48,_zz__zz_decode_REGFILE_WRITE_VALID_ODD_49}}};
  assign _zz__zz_decode_REGFILE_WRITE_VALID_ODD_25 = (decode_INSTRUCTION & 32'h20003014);
  assign _zz__zz_decode_REGFILE_WRITE_VALID_ODD_26 = 32'h20001010;
  assign _zz__zz_decode_REGFILE_WRITE_VALID_ODD_27 = (decode_INSTRUCTION & 32'h20004064);
  assign _zz__zz_decode_REGFILE_WRITE_VALID_ODD_28 = 32'h20004020;
  assign _zz__zz_decode_REGFILE_WRITE_VALID_ODD_32 = (decode_INSTRUCTION & 32'h64003014);
  assign _zz__zz_decode_REGFILE_WRITE_VALID_ODD_33 = 32'h40001010;
  assign _zz__zz_decode_REGFILE_WRITE_VALID_ODD_34 = (decode_INSTRUCTION & 32'h44007014);
  assign _zz__zz_decode_REGFILE_WRITE_VALID_ODD_35 = 32'h00001010;
  assign _zz__zz_decode_REGFILE_WRITE_VALID_ODD_37 = (decode_INSTRUCTION & 32'h00000064);
  assign _zz__zz_decode_REGFILE_WRITE_VALID_ODD_38 = 32'h00000024;
  assign _zz__zz_decode_REGFILE_WRITE_VALID_ODD_40 = ((decode_INSTRUCTION & 32'h00001000) == 32'h00001000);
  assign _zz__zz_decode_REGFILE_WRITE_VALID_ODD_42 = ((decode_INSTRUCTION & 32'h00003000) == 32'h00002000);
  assign _zz__zz_decode_REGFILE_WRITE_VALID_ODD_43 = (|{(_zz__zz_decode_REGFILE_WRITE_VALID_ODD_44 == _zz__zz_decode_REGFILE_WRITE_VALID_ODD_45),(_zz__zz_decode_REGFILE_WRITE_VALID_ODD_46 == _zz__zz_decode_REGFILE_WRITE_VALID_ODD_47)});
  assign _zz__zz_decode_REGFILE_WRITE_VALID_ODD_48 = 1'b0;
  assign _zz__zz_decode_REGFILE_WRITE_VALID_ODD_49 = {(|_zz__zz_decode_REGFILE_WRITE_VALID_ODD_50),{(|_zz__zz_decode_REGFILE_WRITE_VALID_ODD_51),{_zz__zz_decode_REGFILE_WRITE_VALID_ODD_58,{_zz__zz_decode_REGFILE_WRITE_VALID_ODD_61,_zz__zz_decode_REGFILE_WRITE_VALID_ODD_64}}}};
  assign _zz__zz_decode_REGFILE_WRITE_VALID_ODD_44 = (decode_INSTRUCTION & 32'h00002010);
  assign _zz__zz_decode_REGFILE_WRITE_VALID_ODD_45 = 32'h00002000;
  assign _zz__zz_decode_REGFILE_WRITE_VALID_ODD_46 = (decode_INSTRUCTION & 32'h00005000);
  assign _zz__zz_decode_REGFILE_WRITE_VALID_ODD_47 = 32'h00001000;
  assign _zz__zz_decode_REGFILE_WRITE_VALID_ODD_50 = ((decode_INSTRUCTION & 32'h00004048) == 32'h00004008);
  assign _zz__zz_decode_REGFILE_WRITE_VALID_ODD_51 = {_zz_decode_REGFILE_WRITE_VALID_ODD_1,{(_zz__zz_decode_REGFILE_WRITE_VALID_ODD_52 == _zz__zz_decode_REGFILE_WRITE_VALID_ODD_53),{_zz__zz_decode_REGFILE_WRITE_VALID_ODD_54,{_zz__zz_decode_REGFILE_WRITE_VALID_ODD_55,_zz__zz_decode_REGFILE_WRITE_VALID_ODD_57}}}};
  assign _zz__zz_decode_REGFILE_WRITE_VALID_ODD_58 = (|{(_zz__zz_decode_REGFILE_WRITE_VALID_ODD_59 == _zz__zz_decode_REGFILE_WRITE_VALID_ODD_60),_zz_decode_REGFILE_WRITE_VALID_ODD_2});
  assign _zz__zz_decode_REGFILE_WRITE_VALID_ODD_61 = (|(_zz__zz_decode_REGFILE_WRITE_VALID_ODD_62 == _zz__zz_decode_REGFILE_WRITE_VALID_ODD_63));
  assign _zz__zz_decode_REGFILE_WRITE_VALID_ODD_64 = {(|_zz_decode_REGFILE_WRITE_VALID_ODD_6),{(|_zz__zz_decode_REGFILE_WRITE_VALID_ODD_65),{_zz__zz_decode_REGFILE_WRITE_VALID_ODD_74,{_zz__zz_decode_REGFILE_WRITE_VALID_ODD_81,_zz__zz_decode_REGFILE_WRITE_VALID_ODD_84}}}};
  assign _zz__zz_decode_REGFILE_WRITE_VALID_ODD_52 = (decode_INSTRUCTION & 32'h04000024);
  assign _zz__zz_decode_REGFILE_WRITE_VALID_ODD_53 = 32'h04000020;
  assign _zz__zz_decode_REGFILE_WRITE_VALID_ODD_54 = ((decode_INSTRUCTION & 32'h02000024) == 32'h02000020);
  assign _zz__zz_decode_REGFILE_WRITE_VALID_ODD_55 = ((decode_INSTRUCTION & _zz__zz_decode_REGFILE_WRITE_VALID_ODD_56) == 32'h00000020);
  assign _zz__zz_decode_REGFILE_WRITE_VALID_ODD_57 = _zz_decode_REGFILE_WRITE_VALID_ODD_4;
  assign _zz__zz_decode_REGFILE_WRITE_VALID_ODD_59 = (decode_INSTRUCTION & 32'h00000040);
  assign _zz__zz_decode_REGFILE_WRITE_VALID_ODD_60 = 32'h00000040;
  assign _zz__zz_decode_REGFILE_WRITE_VALID_ODD_62 = (decode_INSTRUCTION & 32'h00000020);
  assign _zz__zz_decode_REGFILE_WRITE_VALID_ODD_63 = 32'h00000020;
  assign _zz__zz_decode_REGFILE_WRITE_VALID_ODD_65 = {_zz_decode_REGFILE_WRITE_VALID_ODD_3,{_zz__zz_decode_REGFILE_WRITE_VALID_ODD_66,{_zz__zz_decode_REGFILE_WRITE_VALID_ODD_67,_zz__zz_decode_REGFILE_WRITE_VALID_ODD_69}}};
  assign _zz__zz_decode_REGFILE_WRITE_VALID_ODD_74 = (|{_zz_decode_REGFILE_WRITE_VALID_ODD_6,{_zz__zz_decode_REGFILE_WRITE_VALID_ODD_75,_zz__zz_decode_REGFILE_WRITE_VALID_ODD_76}});
  assign _zz__zz_decode_REGFILE_WRITE_VALID_ODD_81 = (|{_zz__zz_decode_REGFILE_WRITE_VALID_ODD_82,_zz__zz_decode_REGFILE_WRITE_VALID_ODD_83});
  assign _zz__zz_decode_REGFILE_WRITE_VALID_ODD_84 = {(|_zz__zz_decode_REGFILE_WRITE_VALID_ODD_85),{_zz__zz_decode_REGFILE_WRITE_VALID_ODD_88,{_zz__zz_decode_REGFILE_WRITE_VALID_ODD_91,_zz__zz_decode_REGFILE_WRITE_VALID_ODD_93}}};
  assign _zz__zz_decode_REGFILE_WRITE_VALID_ODD_56 = 32'h08000024;
  assign _zz__zz_decode_REGFILE_WRITE_VALID_ODD_66 = ((decode_INSTRUCTION & 32'h00002030) == 32'h00002010);
  assign _zz__zz_decode_REGFILE_WRITE_VALID_ODD_67 = ((decode_INSTRUCTION & _zz__zz_decode_REGFILE_WRITE_VALID_ODD_68) == 32'h00002020);
  assign _zz__zz_decode_REGFILE_WRITE_VALID_ODD_69 = {(_zz__zz_decode_REGFILE_WRITE_VALID_ODD_70 == _zz__zz_decode_REGFILE_WRITE_VALID_ODD_71),(_zz__zz_decode_REGFILE_WRITE_VALID_ODD_72 == _zz__zz_decode_REGFILE_WRITE_VALID_ODD_73)};
  assign _zz__zz_decode_REGFILE_WRITE_VALID_ODD_75 = _zz_decode_REGFILE_WRITE_VALID_ODD_5;
  assign _zz__zz_decode_REGFILE_WRITE_VALID_ODD_76 = {(_zz__zz_decode_REGFILE_WRITE_VALID_ODD_77 == _zz__zz_decode_REGFILE_WRITE_VALID_ODD_78),(_zz__zz_decode_REGFILE_WRITE_VALID_ODD_79 == _zz__zz_decode_REGFILE_WRITE_VALID_ODD_80)};
  assign _zz__zz_decode_REGFILE_WRITE_VALID_ODD_82 = _zz_decode_REGFILE_WRITE_VALID_ODD_3;
  assign _zz__zz_decode_REGFILE_WRITE_VALID_ODD_83 = _zz_decode_REGFILE_WRITE_VALID_ODD_4;
  assign _zz__zz_decode_REGFILE_WRITE_VALID_ODD_85 = {_zz_decode_REGFILE_WRITE_VALID_ODD_3,(_zz__zz_decode_REGFILE_WRITE_VALID_ODD_86 == _zz__zz_decode_REGFILE_WRITE_VALID_ODD_87)};
  assign _zz__zz_decode_REGFILE_WRITE_VALID_ODD_88 = (|(_zz__zz_decode_REGFILE_WRITE_VALID_ODD_89 == _zz__zz_decode_REGFILE_WRITE_VALID_ODD_90));
  assign _zz__zz_decode_REGFILE_WRITE_VALID_ODD_91 = (|_zz__zz_decode_REGFILE_WRITE_VALID_ODD_92);
  assign _zz__zz_decode_REGFILE_WRITE_VALID_ODD_93 = {(|_zz__zz_decode_REGFILE_WRITE_VALID_ODD_94),{_zz__zz_decode_REGFILE_WRITE_VALID_ODD_96,{_zz__zz_decode_REGFILE_WRITE_VALID_ODD_98,_zz__zz_decode_REGFILE_WRITE_VALID_ODD_101}}};
  assign _zz__zz_decode_REGFILE_WRITE_VALID_ODD_68 = 32'h08002020;
  assign _zz__zz_decode_REGFILE_WRITE_VALID_ODD_70 = (decode_INSTRUCTION & 32'h00001030);
  assign _zz__zz_decode_REGFILE_WRITE_VALID_ODD_71 = 32'h00000010;
  assign _zz__zz_decode_REGFILE_WRITE_VALID_ODD_72 = (decode_INSTRUCTION & 32'h28001020);
  assign _zz__zz_decode_REGFILE_WRITE_VALID_ODD_73 = 32'h00000020;
  assign _zz__zz_decode_REGFILE_WRITE_VALID_ODD_77 = (decode_INSTRUCTION & 32'h0000000c);
  assign _zz__zz_decode_REGFILE_WRITE_VALID_ODD_78 = 32'h00000004;
  assign _zz__zz_decode_REGFILE_WRITE_VALID_ODD_79 = (decode_INSTRUCTION & 32'h00000028);
  assign _zz__zz_decode_REGFILE_WRITE_VALID_ODD_80 = 32'h0;
  assign _zz__zz_decode_REGFILE_WRITE_VALID_ODD_86 = (decode_INSTRUCTION & 32'h00000020);
  assign _zz__zz_decode_REGFILE_WRITE_VALID_ODD_87 = 32'h0;
  assign _zz__zz_decode_REGFILE_WRITE_VALID_ODD_89 = (decode_INSTRUCTION & 32'h00004014);
  assign _zz__zz_decode_REGFILE_WRITE_VALID_ODD_90 = 32'h00004010;
  assign _zz__zz_decode_REGFILE_WRITE_VALID_ODD_92 = ((decode_INSTRUCTION & 32'h00006014) == 32'h00002010);
  assign _zz__zz_decode_REGFILE_WRITE_VALID_ODD_94 = {((decode_INSTRUCTION & _zz__zz_decode_REGFILE_WRITE_VALID_ODD_95) == 32'h0),_zz_decode_REGFILE_WRITE_VALID_ODD_2};
  assign _zz__zz_decode_REGFILE_WRITE_VALID_ODD_96 = (|((decode_INSTRUCTION & _zz__zz_decode_REGFILE_WRITE_VALID_ODD_97) == 32'h0));
  assign _zz__zz_decode_REGFILE_WRITE_VALID_ODD_98 = (|{_zz_decode_REGFILE_WRITE_VALID_ODD_1,{_zz__zz_decode_REGFILE_WRITE_VALID_ODD_99,_zz__zz_decode_REGFILE_WRITE_VALID_ODD_100}});
  assign _zz__zz_decode_REGFILE_WRITE_VALID_ODD_101 = {(|_zz__zz_decode_REGFILE_WRITE_VALID_ODD_102),{(|_zz__zz_decode_REGFILE_WRITE_VALID_ODD_103),(|_zz__zz_decode_REGFILE_WRITE_VALID_ODD_104)}};
  assign _zz__zz_decode_REGFILE_WRITE_VALID_ODD_95 = 32'h00000004;
  assign _zz__zz_decode_REGFILE_WRITE_VALID_ODD_97 = 32'h00000058;
  assign _zz__zz_decode_REGFILE_WRITE_VALID_ODD_99 = ((decode_INSTRUCTION & 32'h00002014) == 32'h00002010);
  assign _zz__zz_decode_REGFILE_WRITE_VALID_ODD_100 = ((decode_INSTRUCTION & 32'h40000034) == 32'h40000030);
  assign _zz__zz_decode_REGFILE_WRITE_VALID_ODD_102 = ((decode_INSTRUCTION & 32'h00000014) == 32'h00000004);
  assign _zz__zz_decode_REGFILE_WRITE_VALID_ODD_103 = ((decode_INSTRUCTION & 32'h00000044) == 32'h00000004);
  assign _zz__zz_decode_REGFILE_WRITE_VALID_ODD_104 = ((decode_INSTRUCTION & 32'h00005048) == 32'h00001008);
  assign _zz_execute_BranchPlugin_branch_src2_6 = execute_INSTRUCTION[31];
  assign _zz_execute_BranchPlugin_branch_src2_7 = execute_INSTRUCTION[31];
  assign _zz_execute_BranchPlugin_branch_src2_8 = execute_INSTRUCTION[7];
  always @(posedge clk) begin
    if(_zz_decode_RegFilePlugin_rs1Data) begin
      _zz_RegFilePlugin_regFile_port0 <= RegFilePlugin_regFile[decode_RegFilePlugin_regFileReadAddress1];
    end
  end

  always @(posedge clk) begin
    if(_zz_decode_RegFilePlugin_rs2Data) begin
      _zz_RegFilePlugin_regFile_port1 <= RegFilePlugin_regFile[decode_RegFilePlugin_regFileReadAddress2];
    end
  end

  always @(posedge clk) begin
    if(_zz_decode_RegFilePlugin_rs3Data) begin
      _zz_RegFilePlugin_regFile_port2 <= RegFilePlugin_regFile[decode_RegFilePlugin_regFileReadAddress3];
    end
  end

  always @(posedge clk) begin
    if(_zz_1) begin
      RegFilePlugin_regFile[lastStageRegFileWrite_payload_address] <= lastStageRegFileWrite_payload_data;
    end
  end

  InstructionCache IBusCachedPlugin_cache (
    .io_flush                              (IBusCachedPlugin_cache_io_flush                           ), //i
    .io_cpu_prefetch_isValid               (IBusCachedPlugin_cache_io_cpu_prefetch_isValid            ), //i
    .io_cpu_prefetch_haltIt                (IBusCachedPlugin_cache_io_cpu_prefetch_haltIt             ), //o
    .io_cpu_prefetch_pc                    (IBusCachedPlugin_iBusRsp_stages_0_input_payload[31:0]     ), //i
    .io_cpu_fetch_isValid                  (IBusCachedPlugin_cache_io_cpu_fetch_isValid               ), //i
    .io_cpu_fetch_isStuck                  (IBusCachedPlugin_cache_io_cpu_fetch_isStuck               ), //i
    .io_cpu_fetch_isRemoved                (IBusCachedPlugin_cache_io_cpu_fetch_isRemoved             ), //i
    .io_cpu_fetch_pc                       (IBusCachedPlugin_iBusRsp_stages_1_input_payload[31:0]     ), //i
    .io_cpu_fetch_data                     (IBusCachedPlugin_cache_io_cpu_fetch_data[31:0]            ), //o
    .io_cpu_fetch_mmuRsp_physicalAddress   (IBusCachedPlugin_mmuBus_rsp_physicalAddress[31:0]         ), //i
    .io_cpu_fetch_mmuRsp_isIoAccess        (IBusCachedPlugin_mmuBus_rsp_isIoAccess                    ), //i
    .io_cpu_fetch_mmuRsp_isPaging          (IBusCachedPlugin_mmuBus_rsp_isPaging                      ), //i
    .io_cpu_fetch_mmuRsp_allowRead         (IBusCachedPlugin_mmuBus_rsp_allowRead                     ), //i
    .io_cpu_fetch_mmuRsp_allowWrite        (IBusCachedPlugin_mmuBus_rsp_allowWrite                    ), //i
    .io_cpu_fetch_mmuRsp_allowExecute      (IBusCachedPlugin_mmuBus_rsp_allowExecute                  ), //i
    .io_cpu_fetch_mmuRsp_exception         (IBusCachedPlugin_mmuBus_rsp_exception                     ), //i
    .io_cpu_fetch_mmuRsp_refilling         (IBusCachedPlugin_mmuBus_rsp_refilling                     ), //i
    .io_cpu_fetch_mmuRsp_bypassTranslation (IBusCachedPlugin_mmuBus_rsp_bypassTranslation             ), //i
    .io_cpu_fetch_physicalAddress          (IBusCachedPlugin_cache_io_cpu_fetch_physicalAddress[31:0] ), //o
    .io_cpu_decode_isValid                 (IBusCachedPlugin_cache_io_cpu_decode_isValid              ), //i
    .io_cpu_decode_isStuck                 (IBusCachedPlugin_cache_io_cpu_decode_isStuck              ), //i
    .io_cpu_decode_pc                      (IBusCachedPlugin_iBusRsp_stages_2_input_payload[31:0]     ), //i
    .io_cpu_decode_physicalAddress         (IBusCachedPlugin_cache_io_cpu_decode_physicalAddress[31:0]), //o
    .io_cpu_decode_data                    (IBusCachedPlugin_cache_io_cpu_decode_data[31:0]           ), //o
    .io_cpu_decode_cacheMiss               (IBusCachedPlugin_cache_io_cpu_decode_cacheMiss            ), //o
    .io_cpu_decode_error                   (IBusCachedPlugin_cache_io_cpu_decode_error                ), //o
    .io_cpu_decode_mmuRefilling            (IBusCachedPlugin_cache_io_cpu_decode_mmuRefilling         ), //o
    .io_cpu_decode_mmuException            (IBusCachedPlugin_cache_io_cpu_decode_mmuException         ), //o
    .io_cpu_decode_isUser                  (1'b0                                                      ), //i
    .io_cpu_fill_valid                     (IBusCachedPlugin_cache_io_cpu_fill_valid                  ), //i
    .io_cpu_fill_payload                   (IBusCachedPlugin_cache_io_cpu_decode_physicalAddress[31:0]), //i
    .io_mem_cmd_valid                      (IBusCachedPlugin_cache_io_mem_cmd_valid                   ), //o
    .io_mem_cmd_ready                      (iBus_cmd_ready                                            ), //i
    .io_mem_cmd_payload_address            (IBusCachedPlugin_cache_io_mem_cmd_payload_address[31:0]   ), //o
    .io_mem_cmd_payload_size               (IBusCachedPlugin_cache_io_mem_cmd_payload_size[2:0]       ), //o
    .io_mem_rsp_valid                      (iBus_rsp_valid                                            ), //i
    .io_mem_rsp_payload_data               (iBus_rsp_payload_data[31:0]                               ), //i
    .io_mem_rsp_payload_error              (iBus_rsp_payload_error                                    ), //i
    .clk                                   (clk                                                       ), //i
    .reset                                 (reset                                                     )  //i
  );
  DataCache dataCache_1 (
    .io_cpu_execute_isValid                 (dataCache_1_io_cpu_execute_isValid               ), //i
    .io_cpu_execute_address                 (dataCache_1_io_cpu_execute_address[31:0]         ), //i
    .io_cpu_execute_haltIt                  (dataCache_1_io_cpu_execute_haltIt                ), //o
    .io_cpu_execute_args_wr                 (execute_MEMORY_WR                                ), //i
    .io_cpu_execute_args_size               (dataCache_1_io_cpu_execute_args_size[2:0]        ), //i
    .io_cpu_execute_args_totalyConsistent   (execute_MEMORY_FORCE_CONSTISTENCY                ), //i
    .io_cpu_execute_refilling               (dataCache_1_io_cpu_execute_refilling             ), //o
    .io_cpu_memory_isValid                  (dataCache_1_io_cpu_memory_isValid                ), //i
    .io_cpu_memory_isStuck                  (memory_arbitration_isStuck                       ), //i
    .io_cpu_memory_isWrite                  (dataCache_1_io_cpu_memory_isWrite                ), //o
    .io_cpu_memory_address                  (dataCache_1_io_cpu_memory_address[31:0]          ), //i
    .io_cpu_memory_mmuRsp_physicalAddress   (DBusCachedPlugin_mmuBus_rsp_physicalAddress[31:0]), //i
    .io_cpu_memory_mmuRsp_isIoAccess        (dataCache_1_io_cpu_memory_mmuRsp_isIoAccess      ), //i
    .io_cpu_memory_mmuRsp_isPaging          (DBusCachedPlugin_mmuBus_rsp_isPaging             ), //i
    .io_cpu_memory_mmuRsp_allowRead         (DBusCachedPlugin_mmuBus_rsp_allowRead            ), //i
    .io_cpu_memory_mmuRsp_allowWrite        (DBusCachedPlugin_mmuBus_rsp_allowWrite           ), //i
    .io_cpu_memory_mmuRsp_allowExecute      (DBusCachedPlugin_mmuBus_rsp_allowExecute         ), //i
    .io_cpu_memory_mmuRsp_exception         (DBusCachedPlugin_mmuBus_rsp_exception            ), //i
    .io_cpu_memory_mmuRsp_refilling         (DBusCachedPlugin_mmuBus_rsp_refilling            ), //i
    .io_cpu_memory_mmuRsp_bypassTranslation (DBusCachedPlugin_mmuBus_rsp_bypassTranslation    ), //i
    .io_cpu_writeBack_isValid               (dataCache_1_io_cpu_writeBack_isValid             ), //i
    .io_cpu_writeBack_isStuck               (writeBack_arbitration_isStuck                    ), //i
    .io_cpu_writeBack_isFiring              (writeBack_arbitration_isFiring                   ), //i
    .io_cpu_writeBack_isUser                (1'b0                                             ), //i
    .io_cpu_writeBack_haltIt                (dataCache_1_io_cpu_writeBack_haltIt              ), //o
    .io_cpu_writeBack_isWrite               (dataCache_1_io_cpu_writeBack_isWrite             ), //o
    .io_cpu_writeBack_storeData             (dataCache_1_io_cpu_writeBack_storeData[127:0]    ), //i
    .io_cpu_writeBack_data                  (dataCache_1_io_cpu_writeBack_data[127:0]         ), //o
    .io_cpu_writeBack_address               (dataCache_1_io_cpu_writeBack_address[31:0]       ), //i
    .io_cpu_writeBack_mmuException          (dataCache_1_io_cpu_writeBack_mmuException        ), //o
    .io_cpu_writeBack_unalignedAccess       (dataCache_1_io_cpu_writeBack_unalignedAccess     ), //o
    .io_cpu_writeBack_accessError           (dataCache_1_io_cpu_writeBack_accessError         ), //o
    .io_cpu_writeBack_keepMemRspData        (dataCache_1_io_cpu_writeBack_keepMemRspData      ), //o
    .io_cpu_writeBack_fence_SW              (dataCache_1_io_cpu_writeBack_fence_SW            ), //i
    .io_cpu_writeBack_fence_SR              (dataCache_1_io_cpu_writeBack_fence_SR            ), //i
    .io_cpu_writeBack_fence_SO              (dataCache_1_io_cpu_writeBack_fence_SO            ), //i
    .io_cpu_writeBack_fence_SI              (dataCache_1_io_cpu_writeBack_fence_SI            ), //i
    .io_cpu_writeBack_fence_PW              (dataCache_1_io_cpu_writeBack_fence_PW            ), //i
    .io_cpu_writeBack_fence_PR              (dataCache_1_io_cpu_writeBack_fence_PR            ), //i
    .io_cpu_writeBack_fence_PO              (dataCache_1_io_cpu_writeBack_fence_PO            ), //i
    .io_cpu_writeBack_fence_PI              (dataCache_1_io_cpu_writeBack_fence_PI            ), //i
    .io_cpu_writeBack_fence_FM              (dataCache_1_io_cpu_writeBack_fence_FM[3:0]       ), //i
    .io_cpu_writeBack_exclusiveOk           (dataCache_1_io_cpu_writeBack_exclusiveOk         ), //o
    .io_cpu_redo                            (dataCache_1_io_cpu_redo                          ), //o
    .io_cpu_flush_valid                     (dataCache_1_io_cpu_flush_valid                   ), //i
    .io_cpu_flush_ready                     (dataCache_1_io_cpu_flush_ready                   ), //o
    .io_mem_cmd_valid                       (dataCache_1_io_mem_cmd_valid                     ), //o
    .io_mem_cmd_ready                       (dataCache_1_io_mem_cmd_ready                     ), //i
    .io_mem_cmd_payload_wr                  (dataCache_1_io_mem_cmd_payload_wr                ), //o
    .io_mem_cmd_payload_uncached            (dataCache_1_io_mem_cmd_payload_uncached          ), //o
    .io_mem_cmd_payload_address             (dataCache_1_io_mem_cmd_payload_address[31:0]     ), //o
    .io_mem_cmd_payload_data                (dataCache_1_io_mem_cmd_payload_data[127:0]       ), //o
    .io_mem_cmd_payload_mask                (dataCache_1_io_mem_cmd_payload_mask[15:0]        ), //o
    .io_mem_cmd_payload_size                (dataCache_1_io_mem_cmd_payload_size[2:0]         ), //o
    .io_mem_cmd_payload_last                (dataCache_1_io_mem_cmd_payload_last              ), //o
    .io_mem_rsp_valid                       (dBus_rsp_regNext_valid                           ), //i
    .io_mem_rsp_payload_aggregated          (dBus_rsp_regNext_payload_aggregated[4:0]         ), //i
    .io_mem_rsp_payload_last                (dBus_rsp_regNext_payload_last                    ), //i
    .io_mem_rsp_payload_data                (dBus_rsp_regNext_payload_data[127:0]             ), //i
    .io_mem_rsp_payload_error               (dBus_rsp_regNext_payload_error                   ), //i
    .clk                                    (clk                                              ), //i
    .reset                                  (reset                                            )  //i
  );
  always @(*) begin
    case(_zz_IBusCachedPlugin_jump_pcLoad_payload_5)
      2'b00 : _zz_IBusCachedPlugin_jump_pcLoad_payload_4 = DBusCachedPlugin_redoBranch_payload;
      2'b01 : _zz_IBusCachedPlugin_jump_pcLoad_payload_4 = BranchPlugin_jumpInterface_payload;
      default : _zz_IBusCachedPlugin_jump_pcLoad_payload_4 = IBusCachedPlugin_predictionJumpInterface_payload;
    endcase
  end

  always @(*) begin
    case(_zz_writeBack_DBusCachedPlugin_rspShifted_1)
      4'b0000 : _zz_writeBack_DBusCachedPlugin_rspShifted = writeBack_DBusCachedPlugin_rspSplits_0;
      4'b0001 : _zz_writeBack_DBusCachedPlugin_rspShifted = writeBack_DBusCachedPlugin_rspSplits_1;
      4'b0010 : _zz_writeBack_DBusCachedPlugin_rspShifted = writeBack_DBusCachedPlugin_rspSplits_2;
      4'b0011 : _zz_writeBack_DBusCachedPlugin_rspShifted = writeBack_DBusCachedPlugin_rspSplits_3;
      4'b0100 : _zz_writeBack_DBusCachedPlugin_rspShifted = writeBack_DBusCachedPlugin_rspSplits_4;
      4'b0101 : _zz_writeBack_DBusCachedPlugin_rspShifted = writeBack_DBusCachedPlugin_rspSplits_5;
      4'b0110 : _zz_writeBack_DBusCachedPlugin_rspShifted = writeBack_DBusCachedPlugin_rspSplits_6;
      4'b0111 : _zz_writeBack_DBusCachedPlugin_rspShifted = writeBack_DBusCachedPlugin_rspSplits_7;
      4'b1000 : _zz_writeBack_DBusCachedPlugin_rspShifted = writeBack_DBusCachedPlugin_rspSplits_8;
      4'b1001 : _zz_writeBack_DBusCachedPlugin_rspShifted = writeBack_DBusCachedPlugin_rspSplits_9;
      4'b1010 : _zz_writeBack_DBusCachedPlugin_rspShifted = writeBack_DBusCachedPlugin_rspSplits_10;
      4'b1011 : _zz_writeBack_DBusCachedPlugin_rspShifted = writeBack_DBusCachedPlugin_rspSplits_11;
      4'b1100 : _zz_writeBack_DBusCachedPlugin_rspShifted = writeBack_DBusCachedPlugin_rspSplits_12;
      4'b1101 : _zz_writeBack_DBusCachedPlugin_rspShifted = writeBack_DBusCachedPlugin_rspSplits_13;
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
    case(_zz_writeBack_DBusCachedPlugin_rspShifted_15)
      1'b0 : _zz_writeBack_DBusCachedPlugin_rspShifted_14 = writeBack_DBusCachedPlugin_rspSplits_7;
      default : _zz_writeBack_DBusCachedPlugin_rspShifted_14 = writeBack_DBusCachedPlugin_rspSplits_15;
    endcase
  end
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
