MelkhiorVintageComputing/SBusFPGA/sbus-to-ztex-gateware-migen/blit_cg6.c

/*
 ~/LITEX/riscv64-unknown-elf-gcc-10.1.0-2020.08.2-x86_64-linux-ubuntu14/bin/riscv64-unknown-elf-gcc -Os -S blit_cg6.c -march=rv32ib -mabi=ilp32 -mstrict-align -fno-builtin-memset -nostdlib -ffreestanding -nostartfiles
 ~/LITEX/riscv64-unknown-elf-gcc-10.1.0-2020.08.2-x86_64-linux-ubuntu14/bin/riscv64-unknown-elf-gcc -Os -o blit -march=rv32ib -mabi=ilp32 -T blit_cg6.lds  -nostartfiles blit_cg6.s
 ~/LITEX/riscv64-unknown-elf-gcc-10.1.0-2020.08.2-x86_64-linux-ubuntu14/bin/riscv64-unknown-elf-objcopy  -O binary -j .text blit blit_cg6.raw
*/

#ifndef HRES
#define HRES 1280
#warning "Using default HRES"
#endif
#ifndef VRES
#define VRES 1024
#warning "Using default VRES"
#endif
#ifndef BASE_FB
#define BASE_FB  0x8FE00000 // FIXME : should be generated ; 2+ MiB of SDRAM as framebuffer
#warning "Using default BASE_FB"
#endif

#define BASE_ROM 0x00410000 // FIXME : should be generated ; 4-64 KiB of Wishbone ROM ? ; also in the LDS file ; also in the Vex config

#define BASE_RAM 0x00420000 // FIXME : should be generated : 4-64 KiB of Wishbone SRAM ? ; also in _start
#define BASE_RAM_SIZE 0x00001000 // FIXME : should be generated : 4-64 KiB of Wishbone SRAM ? ; also in _start

#define BASE_FBC 0x00700000 // mandated by CG6 compatibility

#define mul_HRES(a) ((a) * HRES)

//typedef void (*boot_t)(void);
//typedef void (*start_t)(unsigned short, unsigned short, unsigned short, unsigned short, unsigned short, unsigned short, unsigned short, unsigned short);

typedef unsigned int uint32_t;
typedef unsigned int u_int32_t;

/*
struct control_blitter {
	volatile unsigned int fun;
	volatile unsigned int done;
	volatile unsigned short arg[8];
};
*/

#define FUN_DRAW 0x00000001 // hardwired in cg6_accel.py
#define FUN_BLIT 0x00000002 // hardwired in cg6_accel.py
#define FUN_FONT 0x00000004 // hardwired in cg6_accel.py
#define FUN_DONE_BIT           31
#define FUN_FONT_NEXT_RDY_BIT  30
#define FUN_FONT_NEXT_REQ_BIT  29
#define FUN_FONT_NEXT_DONE_BIT 28
#define FUN_DONE           (1<<FUN_DONE_BIT)
#define FUN_FONT_NEXT_RDY  (1<<FUN_FONT_NEXT_RDY_BIT)
#define FUN_FONT_NEXT_REQ  (1<<FUN_FONT_NEXT_REQ_BIT)
#define FUN_FONT_NEXT_DONE (1<<FUN_FONT_NEXT_DONE_BIT)

/* from NetBSD */
/* bits in FHC register */
#define	FHC_FBID_MASK	0xff000000	/* bits 24..31 are frame buffer ID */
#define	FHC_FBID_SHIFT	24
#define	FHC_REV_MASK	0x00f00000	/* bits 20..23 are revision */
#define	FHC_REV_SHIFT	20
#define	FHC_FROP_DISABLE 0x00080000	/* disable fast rasterops */
#define	FHC_ROW_DISABLE	0x00040000	/* disable row cache */
#define	FHC_SRC_DISABLE	0x00020000	/* disable source cache */
#define	FHC_DST_DISABLE	0x00010000	/* disable destination cache */
#define	FHC_RESET	0x00008000	/* reset FBC */
#define	FHC_XXX0	0x00004000	/* unused */
#define	FHC_LEBO	0x00002000	/* set little endian byte order */
#define	FHC_RES_MASK	0x00001800	/* bits 11&12 are resolution */
#define	FHC_RES_1024	 0x00000000		/* res = 1024x768 */
#define	FHC_RES_1152	 0x00000800		/* res = 1152x900 */
#define	FHC_RES_1280	 0x00001000		/* res = 1280x1024 */
#define	FHC_RES_1600	 0x00001800		/* res = 1600x1200 */
#define	FHC_CPU_MASK	0x00000600	/* bits 9&10 are cpu type */
#define	FHC_CPU_SPARC	 0x00000000		/* cpu = sparc */
#define	FHC_CPU_68020	 0x00000200		/* cpu = 68020 */
#define	FHC_CPU_386	 0x00000400		/* cpu = 80386 */
#define	FHC_CPU_XXX	 0x00000600		/* unused */
#define	FHC_TEST	0x00000100	/* modify TESTX and TESTY */
#define	FHC_TESTX_MASK	0x000000f0	/* bits 4..7 are test window X */
#define	FHC_TESTX_SHIFT	4
#define	FHC_TESTY_MASK	0x0000000f	/* bits 0..3 are test window Y */
#define	FHC_TESTY_SHIFT	0

/* Values for the mode register */
#define CG6_MODE	(										\
					   0x00200000 /* GX_BLIT_SRC */			\
					 | 0x00020000 /* GX_MODE_COLOR8 */		\
					 | 0x00008000 /* GX_DRAW_RENDER */		\
					 | 0x00002000 /* GX_BWRITE0_ENABLE */	\
					 | 0x00001000 /* GX_BWRITE1_DISABLE */	\
					 | 0x00000200 /* GX_BREAD_0 */			\
					 | 0x00000080 /* GX_BDISP_0 */			\
											)
#define CG6_MODE_MASK	(									\
						   0x00300000 /* GX_BLIT_ALL */		\
						 | 0x00060000 /* GX_MODE_ALL */		\
						 | 0x00018000 /* GX_DRAW_ALL */		\
						 | 0x00006000 /* GX_BWRITE0_ALL */	\
						 | 0x00001800 /* GX_BWRITE1_ALL */	\
						 | 0x00000600 /* GX_BREAD_ALL */	\
						 | 0x00000180 /* GX_BDISP_ALL */	\
												)
#define CG6_ROMMODE	(										\
					   0x00200000 /* GX_BLIT_SRC */			\
					 | 0x00020000 /* GX_MODE_COLOR8 */		\
					 | 0x00008000 /* GX_DRAW_RENDER */		\
					 | 0x00001000 /* GX_BWRITE1_DISABLE */	\
					 | 0x00000400 /* GX_BREAD_1 */			\
					 | 0x00000100 /* GX_BDISP_1 */			\
					 | 0x00000040 /* GX_INDEX_MOD */ \
											)

/* Value for the alu register for screen-to-screen copies */
#define CG6_ALU_COPY	(												\
						   0x80000000 /* GX_PLANE_ONES (ignore planemask register) */	\
						 | 0x20000000 /* GX_PIXEL_ONES (ignore pixelmask register) */ \
						 | 0x00800000 /* GX_ATTR_SUPP (function unknown) */	\
						 | 0x00000000 /* GX_RAST_BOOL (function unknown) */	\
						 | 0x00000000 /* GX_PLOT_PLOT (function unknown) */	\
						 | 0x08000000 /* GX_PATTERN_ONES (ignore pattern) */ \
						 | 0x01000000 /* GX_POLYG_OVERLAP (unsure - handle overlap?) */	\
						 | 0x0000cccc /* ALU = src */					\
												)

/* Value for the alu register for region fills */
#define CG6_ALU_FILL	(												\
						   0x80000000 /* GX_PLANE_ONES (ignore planemask register) */	\
						 | 0x20000000 /* GX_PIXEL_ONES (ignore pixelmask register) */ \
						 | 0x00800000 /* GX_ATTR_SUPP (function unknown) */	\
						 | 0x00000000 /* GX_RAST_BOOL (function unknown) */	\
						 | 0x00000000 /* GX_PLOT_PLOT (function unknown) */	\
						 | 0x08000000 /* GX_PATTERN_ONES (ignore pattern) */ \
						 | 0x01000000 /* GX_POLYG_OVERLAP (unsure - handle overlap?) */	\
						 | 0x0000ff00 /* ALU = fg color */				\
												)

/* Value for the alu register for toggling an area */
#define CG6_ALU_FLIP	(												\
						   0x80000000 /* GX_PLANE_ONES (ignore planemask register) */	\
						 | 0x20000000 /* GX_PIXEL_ONES (ignore pixelmask register) */ \
						 | 0x00800000 /* GX_ATTR_SUPP (function unknown) */	\
						 | 0x00000000 /* GX_RAST_BOOL (function unknown) */	\
						 | 0x00000000 /* GX_PLOT_PLOT (function unknown) */	\
						 | 0x08000000 /* GX_PATTERN_ONES (ignore pattern) */ \
						 | 0x01000000 /* GX_POLYG_OVERLAP (unsure - handle overlap?) */	\
						 | 0x00005555 /* ALU = ~dst */					\
												)

/* Value for the alu register used by 501-2325 ROM for BLIT */
#define CG6_ALU_ROMBLIT	(												\
						   0x80000000 /* GX_PLANE_ONES (ignore planemask register) */	\
						 | 0x20000000 /* GX_PIXEL_ONES (ignore pixelmask register) */ \
						 | 0x00800000 /* GX_ATTR_SUPP (function unknown) */	\
						 | 0x00000000 /* GX_RAST_BOOL (function unknown) */	\
						 | 0x00000000 /* GX_PLOT_PLOT (function unknown) */	\
						 | 0x08000000 /* GX_PATTERN_ONES (ignore pattern) */ \
						 | 0x01000000 /* GX_POLYG_OVERLAP (unsure - handle overlap?) */	\
						 | 0x00006c60 /* ALU = ??? */					\
												)


/* rasterops */
#define GX_ROP_CLEAR        0x0
#define GX_ROP_INVERT       0x1
#define GX_ROP_NOOP         0x2
#define GX_ROP_SET          0x3

#define GX_ROP_00_0(rop)    ((rop) << 0)
#define GX_ROP_00_1(rop)    ((rop) << 2)
#define GX_ROP_01_0(rop)    ((rop) << 4)
#define GX_ROP_01_1(rop)    ((rop) << 6)
#define GX_ROP_10_0(rop)    ((rop) << 8)
#define GX_ROP_10_1(rop)    ((rop) << 10)
#define GX_ROP_11_0(rop)    ((rop) << 12)
#define GX_ROP_11_1(rop)    ((rop) << 14)
#define GX_PLOT_PLOT        0x00000000
#define GX_PLOT_UNPLOT      0x00020000
#define GX_RAST_BOOL        0x00000000
#define GX_RAST_LINEAR      0x00040000
#define GX_ATTR_UNSUPP      0x00400000
#define GX_ATTR_SUPP        0x00800000
#define GX_POLYG_OVERLAP    0x01000000
#define GX_POLYG_NONOVERLAP 0x02000000
#define GX_PATTERN_ZEROS    0x04000000
#define GX_PATTERN_ONES     0x08000000
#define GX_PATTERN_MASK     0x0c000000
#define GX_PIXEL_ZEROS      0x10000000
#define GX_PIXEL_ONES       0x20000000
#define GX_PIXEL_MASK       0x30000000
#define GX_PLANE_ZEROS      0x40000000
#define GX_PLANE_ONES       0x80000000
#define GX_PLANE_MASK       0xc0000000
/* rops for bit blit / copy area
   with:
       Plane Mask - use plane mask reg.
       Pixel Mask - use all ones.
       Patt  Mask - use all ones.
*/

#define POLY_O          GX_POLYG_OVERLAP
#define POLY_N          GX_POLYG_NONOVERLAP

#define ROP_STANDARD    (GX_PLANE_MASK |\
                        GX_PIXEL_ONES |\
                        GX_ATTR_SUPP |\
                        GX_RAST_BOOL |\
                        GX_PLOT_PLOT)

/* fg = don't care  bg = don't care */

#define ROP_BLIT(O,I)   (ROP_STANDARD | \
                        GX_PATTERN_ONES |\
                        GX_ROP_11_1(I) |\
                        GX_ROP_11_0(O) |\
                        GX_ROP_10_1(I) |\
                        GX_ROP_10_0(O) |\
                        GX_ROP_01_1(I) |\
                        GX_ROP_01_0(O) |\
                        GX_ROP_00_1(I) |\
                        GX_ROP_00_0(O))

/* fg = fgPixel     bg = don't care */

#define ROP_FILL(O,I)   (ROP_STANDARD | \
                        GX_PATTERN_ONES |\
                        GX_ROP_11_1(I) |\
                        GX_ROP_11_0(I) |\
                        GX_ROP_10_1(I) |\
                        GX_ROP_10_0(I) | \
                        GX_ROP_01_1(O) |\
                        GX_ROP_01_0(O) |\
                        GX_ROP_00_1(O) |\
                        GX_ROP_00_0(O))

/* fg = fgPixel     bg = don't care */
 
#define ROP_STIP(O,I)   (ROP_STANDARD |\
                        GX_ROP_11_1(I) |\
                        GX_ROP_11_0(GX_ROP_NOOP) |\
                        GX_ROP_10_1(I) |\
                        GX_ROP_10_0(GX_ROP_NOOP) | \
                        GX_ROP_01_1(O) |\
                        GX_ROP_01_0(GX_ROP_NOOP) |\
                        GX_ROP_00_1(O) |\
                        GX_ROP_00_0(GX_ROP_NOOP))

/* fg = fgPixel     bg = bgPixel */
                            
#define ROP_OSTP(O,I)   (ROP_STANDARD |\
                        GX_ROP_11_1(I) |\
                        GX_ROP_11_0(I) |\
                        GX_ROP_10_1(I) |\
                        GX_ROP_10_0(O) |\
                        GX_ROP_01_1(O) |\
                        GX_ROP_01_0(I) |\
                        GX_ROP_00_1(O) |\
                        GX_ROP_00_0(O))

#define GX_ROP_USE_PIXELMASK    0x30000000

#define GX_BLT_INPROGRESS       0x20000000


/* status register(s) */
#define GX_EXCEPTION		0x80000000
#define GX_TEC_EXCEPTION	0x40000000
#define GX_FULL                 0x20000000
#define GX_INPROGRESS           0x10000000
#define GX_UNSUPPORTED_ATTR	0x02000000
#define GX_HRMONO		0x01000000
#define GX_OVERFLOW		0x00200000
#define GX_PICK			0x00100000
#define GX_TEC_HIDDEN		0x00040000
#define GX_TEC_INTERSECT	0x00020000
#define GX_TEC_VISIBLE		0x00010000
#define GX_BLIT_HARDWARE	0x00008000	/* hardware can blit this */
#define GX_BLIT_SOFTWARE	0x00004000	/* software must blit this */
#define GX_BLIT_SRC_HIDDEN	0x00002000
#define GX_BLIT_SRC_INTERSECT	0x00001000
#define GX_BLIT_SRC_VISIBLE	0x00000800
#define GX_BLIT_DST_HIDDEN	0x00000400
#define GX_BLIT_DST_INTERSECT	0x00000200
#define GX_BLIT_DST_VISIBLE	0x00000100
#define GX_DRAW_HARDWARE	0x00000010	/* hardware can draw this */
#define GX_DRAW_SOFTAWRE	0x00000008	/* software must draw this */
#define GX_DRAW_HIDDEN		0x00000004
#define GX_DRAW_INTERSECT	0x00000002
#define GX_DRAW_VISIBLE		0x00000001

/* MISC register */
#define GX_INDEX(n)         ((n) << 4)
#define GX_INDEX_ALL        0x00000030
#define GX_INDEX_MOD        0x00000040
#define GX_BDISP_0          0x00000080
#define GX_BDISP_1          0x00000100
#define GX_BDISP_ALL        0x00000180
#define GX_BREAD_0          0x00000200
#define GX_BREAD_1          0x00000400
#define GX_BREAD_ALL        0x00000600
#define GX_BWRITE1_ENABLE   0x00000800
#define GX_BWRITE1_DISABLE  0x00001000
#define GX_BWRITE1_ALL      0x00001800
#define GX_BWRITE0_ENABLE   0x00002000
#define GX_BWRITE0_DISABLE  0x00004000
#define GX_BWRITE0_ALL      0x00006000
#define GX_DRAW_RENDER      0x00008000
#define GX_DRAW_PICK        0x00010000
#define GX_DRAW_ALL         0x00018000
#define GX_MODE_COLOR8      0x00020000
#define GX_MODE_COLOR1      0x00040000
#define GX_MODE_HRMONO      0x00060000
#define GX_MODE_ALL         0x00060000
#define GX_VBLANK           0x00080000
#define GX_BLIT_NOSRC       0x00100000
#define GX_BLIT_SRC         0x00200000
#define GX_BLIT_ALL         0x00300000


/* the FBC, mapped at BASE_FDC */
struct cg6_fbc {
	u_int32_t fbc_config;		/* r/o CONFIG register */
	volatile u_int32_t fbc_mode;	/* mode setting */
	u_int32_t fbc_clip;		/* TEC clip check */
	u_int32_t fbc_pad2[1];
	u_int32_t fbc_s;		/* global status */
	u_int32_t fbc_draw;		/* drawing pipeline status */
	u_int32_t fbc_blit;		/* blitter status */
    u_int32_t fbc_font;		/* pixel transfer register */
	u_int32_t fbc_pad3[24];
	u_int32_t fbc_x0;		/* blitter, src llx */
	u_int32_t fbc_y0;		/* blitter, src lly */
	u_int32_t fbc_pad4[2];
	u_int32_t fbc_x1;		/* blitter, src urx */
	u_int32_t fbc_y1;		/* blitter, src ury */
	u_int32_t fbc_pad5[2];
	u_int32_t fbc_x2;		/* blitter, dst llx */
	u_int32_t fbc_y2;		/* blitter, dst lly */
	u_int32_t fbc_pad6[2];
	u_int32_t fbc_x3;		/* blitter, dst urx */
	u_int32_t fbc_y3;		/* blitter, dst ury */
	u_int32_t fbc_pad7[2];
	u_int32_t fbc_offx;		/* x offset for drawing */
	u_int32_t fbc_offy;		/* y offset for drawing */
	u_int32_t fbc_pad8[2];
	u_int32_t fbc_incx;		/* x offset for drawing */
	u_int32_t fbc_incy;		/* y offset for drawing */
	u_int32_t fbc_pad81[2];
	u_int32_t fbc_clipminx;		/* clip rectangle llx */
	u_int32_t fbc_clipminy;		/* clip rectangle lly */
	u_int32_t fbc_pad9[2];
	u_int32_t fbc_clipmaxx;		/* clip rectangle urx */
	u_int32_t fbc_clipmaxy;		/* clip rectangle ury */
	u_int32_t fbc_pad10[2];
	u_int32_t fbc_fg;		/* fg value for rop */
	u_int32_t fbc_bg;
	volatile u_int32_t fbc_alu;		/* operation to be performed */
	u_int32_t fbc_pm;       /* planemask */
	u_int32_t fbc_pad12[508];
	u_int32_t fbc_arectx;		/* rectangle drawing, x coord */
	u_int32_t fbc_arecty;		/* rectangle drawing, y coord */
	/* actually much more, but nothing more we need */
	// extra stuff
	u_int32_t fbc_pad13[22];
	u_int32_t fbc_arectx_prev;		/* rectangle drawing, x coord */
	u_int32_t fbc_arecty_prev;		/* rectangle drawing, y coord */
	volatile u_int32_t fbc_r5_cmd;
	u_int32_t fbc_pad14;
	volatile u_int32_t fbc_r5_status[4];
    volatile u_int32_t fbc_next_font;
    volatile u_int32_t fbc_next_x0;
    volatile u_int32_t fbc_next_x1;
    volatile u_int32_t fbc_next_y0;
};

//#include "./rvintrin.h"

void from_reset(void) __attribute__ ((noreturn)); // nothrow, 

static inline void flush_cache(void) {
	asm volatile(".word 0x0000500F\n"); // flush the Dcache so that we get updated data
}

typedef unsigned int unsigned_param_type;

static void rectfill(const unsigned_param_type xd,
			  const unsigned_param_type yd,
			  const unsigned_param_type wi,
			  const unsigned_param_type re,
			  const unsigned_param_type color
			  );
static void rectfill_pm(const unsigned_param_type xd,
				 const unsigned_param_type yd,
				 const unsigned_param_type wi,
				 const unsigned_param_type re,
				 const unsigned_param_type color,
				 const unsigned char pm
			  );
static void xorrectfill(const unsigned_param_type xd,
						const unsigned_param_type yd,
						const unsigned_param_type wi,
						const unsigned_param_type re,
						const unsigned_param_type color
						);
static void xorrectfill_pm(const unsigned_param_type xd,
						const unsigned_param_type yd,
						const unsigned_param_type wi,
						const unsigned_param_type re,
						const unsigned_param_type color,
						const unsigned char pm
						);
static void invert(const unsigned_param_type xd,
			const unsigned_param_type yd,
			const unsigned_param_type wi,
			const unsigned_param_type re
			);
static void bitblit(const unsigned_param_type xs,
			 const unsigned_param_type ys,
			 const unsigned_param_type wi,
			 const unsigned_param_type re,
			 const unsigned_param_type xd,
			 const unsigned_param_type yd,
			 const unsigned char pm,
			 const unsigned char gxop
			 );

static void print_hexword(unsigned int v, unsigned int bx, unsigned int by);
static void show_status_on_screen(void);

asm(".global _start\n"
	"_start:\n"
	// ".word 0x0000500F\n" // flush cache ; should not be needed after reset
	//"addi sp,zero,66\n" // 0x0042
	//"slli sp,sp,16\n" // 0x00420000, BASE_RAM
	//"addi a0,zero,1\n" // 0x0001
	//"slli a0,a0,12\n" // 0x00001000, BASE_RAM_SIZE
	//"add sp,sp,a0\n" // SP at the end of the SRAM
	"nop\n"
	"li sp, 0x00420ffc\n" // SP at the end of the SRAM
	//"li a0, 0x00700968\n" // @ of r5_cmd
	//"li a1, 0x00C0FFEE\n"
	//"sw a1, 0(a0)\n"
	"call from_reset\n"
	".size	_start, .-_start\n"
	".align	4\n"
	".globl	_start\n"
	".type	_start, @function\n"
	);

#define imax(a,b) (((a)>(b))?(a):(b))
#define imin(a,b) (((a)<(b))?(a):(b))

//#define TRACE_ON_SCREEN

#define DEBUG
#ifdef DEBUG
#define SHOW_FUN(a) fbc->fbc_r5_status[0] = a
#define SHOW_PC() SHOW_FUN(cmd); do { u_int32_t rd; asm volatile("auipc %[rd], 0" : [rd]"=r"(rd) ) ; fbc->fbc_r5_status[1] = rd; } while (0)
#define SHOW_PC_2VAL(a, b) SHOW_PC(); fbc->fbc_r5_status[2] = a; fbc->fbc_r5_status[3] = b
#else
#define SHOW_FUN(a)
#define SHOW_PC()
#define SHOW_PC_2VAL(a, b)
#endif

/* need some way to have identifiable proc# and multiple struct control_blitter for //ism */
/* First need  to set up essential C stuff like the stack */
/* maybe pass core-id as the first parameter (in a0) to everyone */
/* also need to figure out the non-coherent caches ... */
void from_reset(void) {
	struct cg6_fbc* fbc = (struct cg6_fbc*)BASE_FBC;
	unsigned int cmd = fbc->fbc_r5_cmd;
	unsigned int alu = fbc->fbc_alu;
	unsigned int mode = fbc->fbc_mode;
	unsigned int use_planemask = ((alu & GX_PLANE_MASK) == GX_PLANE_MASK) ? 1 : 0;

	switch (cmd & 0xF) {
	case FUN_DRAW: {
		switch (alu) {
		case CG6_ALU_ROMBLIT: // ____6c60 ROM -> ????
			{
				switch (mode) {
				case (GX_BLIT_SRC |	GX_MODE_COLOR8 | GX_DRAW_RENDER | GX_BWRITE1_DISABLE | GX_BREAD_1 | GX_BDISP_1 | GX_INDEX_MOD ):
					rectfill(fbc->fbc_arectx_prev,
							 fbc->fbc_arecty_prev,
							 1 + fbc->fbc_arectx - fbc->fbc_arectx_prev,
							 1 + fbc->fbc_arecty - fbc->fbc_arecty_prev,
							 fbc->fbc_fg);
					break;
				default:
					SHOW_PC_2VAL(alu, mode);
					break;
				}
			} break;
		case CG6_ALU_FILL:  // ____ff00 console
		case CG6_ALU_COPY:  // ____cccc equivalent to fill if patterns == 1 (... which is the case with GX_PATTERN_ONES)
		case ROP_FILL(GX_ROP_CLEAR,  GX_ROP_SET): // ____ff00 Draw/GXcopy in X11
		case ROP_BLIT(GX_ROP_CLEAR,  GX_ROP_SET): // ____cccc Blit/GXcopy in X11
			{
				switch (mode) {
				case (GX_BLIT_SRC | GX_MODE_COLOR8): // console: rectfill & clearscreen
				case (GX_BLIT_SRC |	GX_MODE_COLOR8 | GX_DRAW_RENDER | GX_BWRITE0_ENABLE | GX_BWRITE1_DISABLE | GX_BREAD_0 | GX_BDISP_0):
					if (use_planemask)
						rectfill_pm(fbc->fbc_arectx_prev,
									fbc->fbc_arecty_prev,
									1 + fbc->fbc_arectx - fbc->fbc_arectx_prev,
									1 + fbc->fbc_arecty - fbc->fbc_arecty_prev,
									fbc->fbc_fg,
									fbc->fbc_pm);
					else
						rectfill(fbc->fbc_arectx_prev,
								 fbc->fbc_arecty_prev,
								 1 + fbc->fbc_arectx - fbc->fbc_arectx_prev,
								 1 + fbc->fbc_arecty - fbc->fbc_arecty_prev,
								 fbc->fbc_fg);
					break;
				default:
					SHOW_PC_2VAL(alu, mode);
					break;
				}
			} break;
		case CG6_ALU_FLIP: { // ____5555 console -> put ~dst everywhere
			switch (mode)
				{
				case (GX_BLIT_SRC | GX_MODE_COLOR8): // invert
					invert(fbc->fbc_arectx_prev,
						   fbc->fbc_arecty_prev,
						   1 + fbc->fbc_arectx - fbc->fbc_arectx_prev,
						   1 + fbc->fbc_arecty - fbc->fbc_arecty_prev);
					break;
				default:
					SHOW_PC_2VAL(alu, mode);
					break;
				}
		} break;
		case ROP_FILL(GX_ROP_NOOP,  GX_ROP_INVERT): { // ____55aa Draw/GXxor in X11 -> put ~dst if src is 1, put dst if src is 0
			switch (mode)
				{
				case (GX_BLIT_SRC |	GX_MODE_COLOR8 | GX_DRAW_RENDER | GX_BWRITE0_ENABLE | GX_BWRITE1_DISABLE | GX_BREAD_0 | GX_BDISP_0):
					if (use_planemask)
						xorrectfill_pm(fbc->fbc_arectx_prev,
									fbc->fbc_arecty_prev,
									1 + fbc->fbc_arectx - fbc->fbc_arectx_prev,
									1 + fbc->fbc_arecty - fbc->fbc_arecty_prev,
									fbc->fbc_fg,
									fbc->fbc_pm);
					else
						xorrectfill(fbc->fbc_arectx_prev,
									fbc->fbc_arecty_prev,
									1 + fbc->fbc_arectx - fbc->fbc_arectx_prev,
									1 + fbc->fbc_arecty - fbc->fbc_arecty_prev,
									fbc->fbc_fg);
						
					break;
				default:
					SHOW_PC_2VAL(alu, mode);
					break;
				}
		} break;
		default:
			SHOW_PC_2VAL(alu, mode);
			break;
		}
	} break;
	case FUN_BLIT: {
		switch (alu)
			{
			case CG6_ALU_ROMBLIT: // ____6c60 ROM -> ????
				{
					switch (mode) {
					case (GX_BLIT_SRC |	GX_MODE_COLOR8 | GX_DRAW_RENDER | GX_BWRITE1_DISABLE | GX_BREAD_1 | GX_BDISP_1 | GX_INDEX_MOD ):
						{
							const unsigned_param_type xs = fbc->fbc_x0;
							const unsigned_param_type ys = fbc->fbc_y0;
							const unsigned_param_type wi = fbc->fbc_x1 - xs + 1;
							const unsigned_param_type re = fbc->fbc_y1 - ys + 1;
							const unsigned_param_type xd = fbc->fbc_x2;
							const unsigned_param_type yd = fbc->fbc_y2;
							const unsigned_param_type wi_dup = fbc->fbc_x3 - xd + 1;
							const unsigned_param_type re_dup = fbc->fbc_y3 - yd + 1;
							bitblit(xs, ys, wi, re, xd, yd, 0xFF, 0x3); // GXcopy
						}
						break;
					default:
						SHOW_PC_2VAL(alu, mode);
						break;
					}
				} break;
			case CG6_ALU_COPY: // ____cccc console -> put the src
			case ROP_BLIT(GX_ROP_CLEAR,  GX_ROP_SET): // ____ff00 Blit/GXcopy in X11 -> put 1 if src is 1, put 0 if src is 0 (!)
				{
					switch (mode) {
					case (GX_BLIT_SRC | GX_MODE_COLOR8): // console
					case (GX_BLIT_SRC |	GX_MODE_COLOR8 | GX_DRAW_RENDER | GX_BWRITE0_ENABLE | GX_BWRITE1_DISABLE | GX_BREAD_0 | GX_BDISP_0):
						{
							const unsigned_param_type xs = fbc->fbc_x0;
							const unsigned_param_type ys = fbc->fbc_y0;
							const unsigned_param_type wi = fbc->fbc_x1 - xs + 1;
							const unsigned_param_type re = fbc->fbc_y1 - ys + 1;
							const unsigned_param_type xd = fbc->fbc_x2;
							const unsigned_param_type yd = fbc->fbc_y2;
							const unsigned_param_type wi_dup = fbc->fbc_x3 - xd + 1;
							const unsigned_param_type re_dup = fbc->fbc_y3 - yd + 1;
							if (use_planemask)
								bitblit(xs, ys, wi, re, xd, yd, fbc->fbc_pm, 0x3); // GXcopy
							else
								bitblit(xs, ys, wi, re, xd, yd, 0xFF, 0x3); // GXcopy
						}
						break;
					default:
						SHOW_PC_2VAL(alu, mode);
						break;
					}	  
				} break;
			case ROP_BLIT(GX_ROP_SET,  GX_ROP_SET): // ____ffff Blit/GXset in X11 -> put 1 everywhere
				{
					switch (mode) {
					case (GX_BLIT_SRC | GX_MODE_COLOR8): // console
					case (GX_BLIT_SRC |	GX_MODE_COLOR8 | GX_DRAW_RENDER | GX_BWRITE0_ENABLE | GX_BWRITE1_DISABLE | GX_BREAD_0 | GX_BDISP_0):
						{
							const unsigned_param_type xs = fbc->fbc_x0;
							const unsigned_param_type ys = fbc->fbc_y0;
							const unsigned_param_type wi = fbc->fbc_x1 - xs + 1;
							const unsigned_param_type re = fbc->fbc_y1 - ys + 1;
							const unsigned_param_type xd = fbc->fbc_x2;
							const unsigned_param_type yd = fbc->fbc_y2;
							const unsigned_param_type wi_dup = fbc->fbc_x3 - xd + 1;
							const unsigned_param_type re_dup = fbc->fbc_y3 - yd + 1;
							if (use_planemask)
								rectfill_pm(xd, yd, wi, re, 0xff, fbc->fbc_pm); // GXset doesn't need the source ???
							else
								rectfill(xd, yd, wi, re, 0xff); // GXset doesn't need the source ???
						}
						break;
					default:
						SHOW_PC_2VAL(alu, mode);
						break;
					}	  
				} break;
			case ROP_BLIT(GX_ROP_NOOP,  GX_ROP_INVERT): // ____6666 Blit/GXxor in X11 -> xor everywhere
				{
					switch (mode) {
					case (GX_BLIT_SRC |	GX_MODE_COLOR8 | GX_DRAW_RENDER | GX_BWRITE0_ENABLE | GX_BWRITE1_DISABLE | GX_BREAD_0 | GX_BDISP_0):
						{
							const unsigned_param_type xs = fbc->fbc_x0;
							const unsigned_param_type ys = fbc->fbc_y0;
							const unsigned_param_type wi = fbc->fbc_x1 - xs + 1;
							const unsigned_param_type re = fbc->fbc_y1 - ys + 1;
							const unsigned_param_type xd = fbc->fbc_x2;
							const unsigned_param_type yd = fbc->fbc_y2;
							const unsigned_param_type wi_dup = fbc->fbc_x3 - xd + 1;
							const unsigned_param_type re_dup = fbc->fbc_y3 - yd + 1;
							if (use_planemask)
								bitblit(xs, ys, wi, re, xd, yd, fbc->fbc_pm, 0x6); // GXor
							else
								bitblit(xs, ys, wi, re, xd, yd, 0xFF, 0x6); // GXor
						}
						break;
					
					default:
						SHOW_PC_2VAL(alu, mode);
						break;
					}
				} break;
			default:
				SHOW_PC_2VAL(alu, mode);
				break;
			}
	} break;
	case FUN_FONT:
		{
			switch (alu)
				{
				case CG6_ALU_COPY: // console
				case ROP_BLIT(GX_ROP_CLEAR,  GX_ROP_SET): // Blit/GXcopy in X11
					{
						switch (mode) {
						case (GX_BLIT_NOSRC | GX_MODE_COLOR8): // console
						case (GX_BLIT_NOSRC | GX_MODE_COLOR8 | GX_DRAW_RENDER | GX_BWRITE0_ENABLE | GX_BWRITE1_DISABLE | GX_BREAD_0 | GX_BDISP_0):
							//case (GX_BLIT_SRC | GX_MODE_COLOR8): // what is SRC then?
							{
								// cgsix_putchar_aa
								// Cg6UploadToScreen
								const unsigned int xdsm = fbc->fbc_clipminx;
								const unsigned int xdem = fbc->fbc_clipmaxx;
								do {
									while ((cmd & FUN_FONT_NEXT_RDY) == 0) {
										if ((cmd & FUN_FONT_NEXT_DONE) != 0)
											goto finish;
										cmd = fbc->fbc_r5_cmd;
									}
									const unsigned int xdsr = fbc->fbc_next_x0;
									const unsigned int xds =  imax(xdsr, xdsm);
									const unsigned int xder = fbc->fbc_next_x1;
									const unsigned int xde =  imin(xder, xdem);
									const unsigned int yd =   fbc->fbc_next_y0;
									const unsigned int we =   xde - xdsr + 1;
									const unsigned int xoff = xds - xdsr;
									if ((xoff == 0) && (we == 4) && ((xdsr & 0x3) == 0)) {
										unsigned char *dptr = (((unsigned char *)BASE_FB) + mul_HRES(yd) + xdsr);
										unsigned int bits = fbc->fbc_next_font;
										unsigned int rbits;
										asm("rev8 %0, %1\n" : "=r"(rbits) : "r"(bits));
										*((unsigned int*)dptr) = rbits;
									} else if ((xde >= xds) && (xoff<we)) {
										unsigned int bits = fbc->fbc_next_font;
#if 1
										unsigned int rbits;
										asm("rev8 %0, %1\n" : "=r"(rbits) : "r"(bits));
#endif
										unsigned char *dptr = (((unsigned char *)BASE_FB) + mul_HRES(yd) + xdsr);
										for (unsigned i = xoff ; i < we ; i++) {
#if 0
											unsigned char data = (bits >> (((we-1)-i) * 8)) & 0xFF;
											dptr[i] = data;
#else
											dptr[i] = (unsigned char)rbits;
											rbits >>= 8;
#endif
										}
									}
									cmd = (FUN_FONT_NEXT_REQ | FUN_FONT);
									fbc->fbc_r5_cmd = cmd;
								} while (1);
							}
							break;
						default:
							SHOW_PC_2VAL(alu, mode);
							break;
						}	  
					} break;
				case (GX_PATTERN_ONES | ROP_OSTP(GX_ROP_CLEAR, GX_ROP_SET)): // ____fc30 console, also X11 OpaqueStipple/GXcopy FIXME:planemask?
					{
						switch (mode) {
						case (GX_BLIT_NOSRC | GX_MODE_COLOR1):
							{
								const unsigned int xdsm = fbc->fbc_clipminx;
								const unsigned int xdem = fbc->fbc_clipmaxx;
								// cgsix_putchar
								do {
									while ((cmd & FUN_FONT_NEXT_RDY) == 0) {
										if ((cmd & FUN_FONT_NEXT_DONE) != 0)
											goto finish;
										cmd = fbc->fbc_r5_cmd;
									}
									const unsigned int xdsr = fbc->fbc_next_x0;
									const unsigned int xds =  imax(xdsr, xdsm);
									const unsigned int xder = fbc->fbc_next_x1;
									const unsigned int xde =  imin(xder,xdem);
									const unsigned int yd =   fbc->fbc_next_y0;
									const unsigned int we =   xde - xdsr + 1;
									const unsigned int xoff = xds - xdsr;
									const unsigned char fg8 = (unsigned char)(fbc->fbc_fg & 0xFF);
									const unsigned char bg8 = (unsigned char)(fbc->fbc_bg & 0xFF);
									if ((xde >= xds) && (xoff<we)) {
										unsigned int bits = fbc->fbc_next_font << xoff;
										unsigned char *dptr = (((unsigned char *)BASE_FB) + mul_HRES(yd) + xdsr);
										for (unsigned i = xoff ; i < we ; i++) {
#if 0
											if (bits & 0x80000000) dptr[i] = fg8; else dptr[i] = bg8;
#else
											unsigned char data;
											asm("cmov %0, %1, %2, %3\n" : "=r"(data) : "r"(bits&0x80000000), "r"(fg8), "r"(bg8));
											dptr[i] = data;
#endif
											bits <<= 1;
										}
									}
									cmd = (FUN_FONT_NEXT_REQ | FUN_FONT);
									fbc->fbc_r5_cmd = cmd;
								} while (1);
							}
							break;
						default:
							SHOW_PC_2VAL(alu, mode);
							break;
						}	  
					} break;
				case (GX_PATTERN_ONES | ROP_STIP(GX_ROP_CLEAR, GX_ROP_SET)): // X11 Stipple/GXcopy (not used in console) FIXME:planemask?
					{
						switch (mode)
							{
							case (GX_BLIT_NOSRC | GX_MODE_COLOR1):
								{
									const unsigned int xdsm = fbc->fbc_clipminx;
									const unsigned int xdem = fbc->fbc_clipmaxx;
									// cgsix_putchar
									do {
										while ((cmd & FUN_FONT_NEXT_RDY) == 0) {
											if ((cmd & FUN_FONT_NEXT_DONE) != 0)
												goto finish;
											cmd = fbc->fbc_r5_cmd;
										}
										const unsigned int xdsr = fbc->fbc_next_x0;
										const unsigned int xds =  imax(xdsr, xdsm);
										const unsigned int xder = fbc->fbc_next_x1;
										const unsigned int xde =  imin(xder,xdem);
										const unsigned int yd =   fbc->fbc_next_y0;
										const unsigned int we =   xde - xdsr + 1;
										const unsigned int xoff = xds - xdsr;
										const unsigned char fg8 = (unsigned char)(fbc->fbc_fg & 0xFF);
										//const unsigned char bg8 = (unsigned char)(fbc->fbc_bg & 0xFF);
										if ((xde >= xds) && (xoff<we)) {
											unsigned int bits = fbc->fbc_next_font << xoff;
											unsigned char *dptr = (((unsigned char *)BASE_FB) + mul_HRES(yd) + xdsr);
											for (unsigned i = xoff ; i < we ; i++) {
												if (bits & 0x80000000) dptr[i] = fg8;
												bits <<= 1;
											}
										}
										cmd = (FUN_FONT_NEXT_REQ | FUN_FONT);
										fbc->fbc_r5_cmd = cmd;
									} while (1);
								}
								break;
							default:
								SHOW_PC_2VAL(alu, mode);
								break;
							}	  
					} break;
				default:
					SHOW_PC_2VAL(alu, mode);
					break;
				}
		} break;
	default:
		break;
	}

 finish:
#ifdef TRACE_ON_SCREEN
	show_status_on_screen();
#endif
	
	// make sure we have nothing left in the cache
	flush_cache();

	fbc->fbc_r5_cmd = FUN_DONE;

 done:
	/* wait for reset */
	goto done;
}

#define bitblit_proto_int(a, b, suf)									\
	static void bitblit##a##b##suf(const unsigned_param_type xs,		\
							const unsigned_param_type ys,				\
							const unsigned_param_type wi,				\
							const unsigned_param_type re,				\
							const unsigned_param_type xd,				\
							const unsigned_param_type yd,				\
							const unsigned char pm						\
							)
#define bitblit_proto(suf)						\
	bitblit_proto_int(_fwd, _fwd, suf);			\
	bitblit_proto_int(_bwd, _fwd, suf);			\
	bitblit_proto_int(_fwd, _bwd, suf)
//	bitblit_proto_int(_bwd, _bwd, suf);

bitblit_proto(_copy);
bitblit_proto(_xor);
bitblit_proto(_copy_pm);
bitblit_proto(_xor_pm);


#define ROUTE_BITBLIT_PM(pm, bb)					\
	if (pm == 0xFF) bb(xs, ys, wi, re, xd, yd, pm); \
	else bb##_pm(xs, ys, wi, re, xd, yd, pm)

static void bitblit(const unsigned_param_type xs,
			 const unsigned_param_type ys,
			 const unsigned_param_type wi,
			 const unsigned_param_type re,
			 const unsigned_param_type xd,
			 const unsigned_param_type yd,
			 const unsigned char pm,
			 const unsigned char gxop
			 ) {
	struct cg6_fbc* fbc = (struct cg6_fbc*)BASE_FBC;
	
	if (ys > yd) {
		switch(gxop) {
		case 0x3: // GXcopy
			ROUTE_BITBLIT_PM(pm, bitblit_fwd_fwd_copy);
			break;
		case 0x6: // GXxor
			ROUTE_BITBLIT_PM(pm, bitblit_fwd_fwd_xor);
			break;
		}
	} else if (ys < yd) {
		switch(gxop) {
		case 0x3: // GXcopy
			ROUTE_BITBLIT_PM(pm, bitblit_bwd_fwd_copy);
			break;
		case 0x6: // GXxor
			ROUTE_BITBLIT_PM(pm, bitblit_bwd_fwd_xor);
			break;
		}
	} else { // ys == yd
		if (xs > xd) {
			switch(gxop) {
			case 0x3: // GXcopy
				ROUTE_BITBLIT_PM(pm, bitblit_fwd_fwd_copy);
				break;
			case 0x6: // GXxor
				ROUTE_BITBLIT_PM(pm, bitblit_fwd_fwd_xor);
				break;
			}
		} else if (xs < xd) {
			switch(gxop) {
			case 0x3: // GXcopy
				ROUTE_BITBLIT_PM(pm, bitblit_fwd_bwd_copy);
				break;
			case 0x6: // GXxor
				ROUTE_BITBLIT_PM(pm, bitblit_fwd_bwd_xor);
				break;
			}
		} else { // xs == xd
			switch(gxop) {
			case 0x3: // GXcopy
				/* don't bother */
				break;
			case 0x6:  // GXxor
				rectfill_pm(xd, yd, wi, re, 0, pm);
				break;
			}
		}
	}
 }


static void rectfill(const unsigned_param_type xd,
			  const unsigned_param_type yd,
			  const unsigned_param_type wi,
			  const unsigned_param_type re,
			  const unsigned_param_type color
			  ) {
	struct cg6_fbc* fbc = (struct cg6_fbc*)BASE_FBC;
	unsigned int i, j;
	unsigned char *dptr = (((unsigned char *)BASE_FB) + mul_HRES(yd) + xd);
	unsigned char *dptr_line = dptr;
	unsigned char u8color = color & 0xFF;

	for (j = 0 ; j < re ; j++) {
		unsigned char *dptr_elt = dptr_line;
		i = 0;
		for ( ; i < wi && ((unsigned int)dptr_elt&0x3)!=0; i++) {
			*dptr_elt = u8color;
			dptr_elt ++;
		}
		if (wi > 3) {
			unsigned int u32color = (unsigned int)u8color | ((unsigned int)u8color)<<8 | ((unsigned int)u8color)<<16 | ((unsigned int)u8color)<<24;
			for ( ; i < (wi-3) ; i+=4) {
				*(unsigned int*)dptr_elt = u32color;
				dptr_elt +=4;
			}
		}	
		for ( ; i < wi ; i++) {
			*dptr_elt = u8color;
			dptr_elt ++;
		}
		dptr_line += HRES;
	}
}

static void rectfill_pm(const unsigned_param_type xd,
				 const unsigned_param_type yd,
				 const unsigned_param_type wi,
				 const unsigned_param_type re,
				 const unsigned_param_type color,
				 const unsigned char pm
			  ) {
	struct cg6_fbc* fbc = (struct cg6_fbc*)BASE_FBC;
	unsigned int i, j;
	unsigned char *dptr = (((unsigned char *)BASE_FB) + mul_HRES(yd) + xd);
	unsigned char *dptr_line = dptr;
	unsigned char u8color = color;

	for (j = 0 ; j < re ; j++) {
		unsigned char *dptr_elt = dptr_line;
		i = 0;
		for ( ; i < wi && ((unsigned int)dptr_elt&0x3)!=0; i++) {
			*dptr_elt = (u8color & pm) | (*dptr_elt & ~pm);
			dptr_elt ++;
		}
		if (wi > 3) {
			unsigned int u32color = (unsigned int)u8color | ((unsigned int)u8color)<<8 | ((unsigned int)u8color)<<16 | ((unsigned int)u8color)<<24;
			unsigned int u32pm = (unsigned int)pm | ((unsigned int)pm)<<8 | ((unsigned int)pm)<<16 | ((unsigned int)pm)<<24;
			for ( ; i < (wi-3) ; i+=4) {
				*(unsigned int*)dptr_elt = (u32color & u32pm) | (*(unsigned int*)dptr_elt & ~u32pm);
				dptr_elt +=4;
			}
		}
		for ( ; i < wi ; i++) {
			*dptr_elt = (u8color & pm) | (*dptr_elt & ~pm);
			dptr_elt ++;
		}
		dptr_line += HRES;
	}
}


static void xorrectfill(const unsigned_param_type xd,
			  const unsigned_param_type yd,
			  const unsigned_param_type wi,
			  const unsigned_param_type re,
			  const unsigned_param_type color
			  ) {
	struct cg6_fbc* fbc = (struct cg6_fbc*)BASE_FBC;
	unsigned int i, j;
	unsigned char *dptr = (((unsigned char *)BASE_FB) + mul_HRES(yd) + xd);
	unsigned char *dptr_line = dptr;
	unsigned char u8color = color & 0xFF;

	for (j = 0 ; j < re ; j++) {
		unsigned char *dptr_elt = dptr_line;
		i = 0;
		for ( ; i < wi && ((unsigned int)dptr_elt&0x3)!=0; i++) {
			*dptr_elt ^= u8color;
			dptr_elt ++;
		}
		if (wi > 3) {
			unsigned int u32color = (unsigned int)u8color | ((unsigned int)u8color)<<8 | ((unsigned int)u8color)<<16 | ((unsigned int)u8color)<<24;
			for ( ; i < (wi-3) ; i+=4) {
				*(unsigned int*)dptr_elt ^= u32color;
				dptr_elt +=4;
			}
		}	
		for ( ; i < wi ; i++) {
			*dptr_elt ^= u8color;
			dptr_elt ++;
		}
		dptr_line += HRES;
	}
}
static void xorrectfill_pm(const unsigned_param_type xd,
				 const unsigned_param_type yd,
				 const unsigned_param_type wi,
				 const unsigned_param_type re,
				 const unsigned_param_type color,
				 const unsigned char pm
			  ) {
	struct cg6_fbc* fbc = (struct cg6_fbc*)BASE_FBC;
	unsigned int i, j;
	unsigned char *dptr = (((unsigned char *)BASE_FB) + mul_HRES(yd) + xd);
	unsigned char *dptr_line = dptr;
	unsigned char u8color = color;

	for (j = 0 ; j < re ; j++) {
		unsigned char *dptr_elt = dptr_line;
		i = 0;
		for ( ; i < wi && ((unsigned int)dptr_elt&0x3)!=0; i++) {
			*dptr_elt ^= (u8color & pm);
			dptr_elt ++;
		}
		if (wi > 3) {
			unsigned int u32color = (unsigned int)u8color | ((unsigned int)u8color)<<8 | ((unsigned int)u8color)<<16 | ((unsigned int)u8color)<<24;
			unsigned int u32pm = (unsigned int)pm | ((unsigned int)pm)<<8 | ((unsigned int)pm)<<16 | ((unsigned int)pm)<<24;
			for ( ; i < (wi-3) ; i+=4) {
				*(unsigned int*)dptr_elt ^= (u32color & u32pm);
				dptr_elt +=4;
			}
		}
		for ( ; i < wi ; i++) {
			*dptr_elt ^= (u8color & pm);
			dptr_elt ++;
		}
		dptr_line += HRES;
	}
}

static void invert(const unsigned_param_type xd,
			const unsigned_param_type yd,
			const unsigned_param_type wi,
			const unsigned_param_type re
			) {
	struct cg6_fbc* fbc = (struct cg6_fbc*)BASE_FBC;
	unsigned int i, j;
	unsigned char *dptr = (((unsigned char *)BASE_FB) + mul_HRES(yd) + xd);
	unsigned char *dptr_line = dptr;
	
	for (j = 0 ; j < re ; j++) {
		unsigned char *dptr_elt = dptr_line;
		i = 0;
		for ( ; i < wi && ((unsigned int)dptr_elt&0x3)!=0; i++) {
			*dptr_elt = ~(*dptr_elt);
			dptr_elt ++;
		}
		if (wi > 3) {
			for ( ; i < (wi-3) ; i+=4) {
				*(unsigned int*)dptr_elt = ~(*(unsigned int*)dptr_elt);
				dptr_elt +=4;
			}
		}
		for ( ; i < wi ; i++) {
			*dptr_elt = ~(*dptr_elt);
			dptr_elt ++;
		}
		dptr_line += HRES;
	}
}


// NOT using npm enables the use of 'cmix' in more cases
#define COPY(d,s,pm,npm) (d) = (s)
//#define COPY_PM(d,s,pm,npm) (d) = (((s) & (pm)) | ((d) & (npm)))
#define COPY_PM(d,s,pm,npm) (d) = (((s) & (pm)) | ((d) & (~pm)))
#define XOR(d,s,pm,npm) (d) = ((s) ^ (d))
//#define XOR_PM(d,s,pm,npm) (d) = ((((s) ^ (d)) & (pm)) | ((d) & (npm)))
#define XOR_PM(d,s,pm,npm) (d) = ((((s) ^ (d)) & (pm)) | ((d) & (~pm)))

#define BLIT_FWD_FWD(NAME, OP)											\
	static void bitblit_fwd_fwd_##NAME(const unsigned_param_type xs,	\
									   const unsigned_param_type ys,	\
									   const unsigned_param_type wi,	\
									   const unsigned_param_type re,	\
									   const unsigned_param_type xd,	\
									   const unsigned_param_type yd,	\
									   const unsigned char pm) {		\
	unsigned int i, j;													\
	unsigned char *sptr = (((unsigned char *)BASE_FB) + mul_HRES(ys) + xs); \
	unsigned char *dptr = (((unsigned char *)BASE_FB) + mul_HRES(yd) + xd); \
	unsigned char *sptr_line = sptr;									\
	unsigned char *dptr_line = dptr;									\
	/*const unsigned char npm = ~pm;*/									\
																		\
	for (j = 0 ; j < re ; j++) {										\
		unsigned char *sptr_elt = sptr_line;							\
		unsigned char *dptr_elt = dptr_line;							\
		i = 0;															\
		if (wi>3) {														\
			if ((xs & 0x3) || (xd & 0x3)) {								\
				for ( ; i < wi && ((unsigned int)dptr_elt&0x3)!=0; i++) { \
					OP(*dptr_elt, *sptr_elt, pm, npm);					\
					dptr_elt ++;										\
					sptr_elt ++;										\
				}														\
				unsigned char *sptr_elt_al = (unsigned char*)((unsigned int)sptr_elt & ~0x3); \
				unsigned int fsr_cst = 8*((unsigned int)sptr_elt & 0x3); \
				unsigned int src0 = ((unsigned int*)sptr_elt_al)[0];	\
				unsigned int u32pm = (unsigned int)pm | ((unsigned int)pm)<<8 | ((unsigned int)pm)<<16 | ((unsigned int)pm)<<24; \
				for ( ; i < (wi-3) ; i+=4) {							\
					unsigned int src1 = ((unsigned int*)sptr_elt_al)[1]; \
					unsigned int val;									\
					asm("fsr %0, %1, %2, %3\n" : "=r"(val) : "r"(src0), "r"(src1), "r"(fsr_cst)); \
					OP(*(unsigned int*)dptr_elt, val, u32pm, u32npm);	\
					src0 = src1;										\
					dptr_elt += 4;										\
					sptr_elt_al += 4;									\
				}														\
				sptr_elt = sptr_elt_al + ((unsigned int)sptr_elt & 0x3); \
			} else {													\
				const unsigned int u32pm = (unsigned int)pm | ((unsigned int)pm)<<8 | ((unsigned int)pm)<<16 | ((unsigned int)pm)<<24; \
				/*const unsigned int u32npm = (unsigned int)npm | ((unsigned int)npm)<<8 | ((unsigned int)npm)<<16 | ((unsigned int)npm)<<24;*/ \
				if (((xs & 0xf) == 0) && ((xd & 0xf) == 0)) {			\
					for ( ; i < (wi&(~0xf)) ; i+= 16) {					\
						OP(((unsigned int*)dptr_elt)[0], ((unsigned int*)sptr_elt)[0], u32pm, u32npm); \
						OP(((unsigned int*)dptr_elt)[1], ((unsigned int*)sptr_elt)[1], u32pm, u32npm); \
						OP(((unsigned int*)dptr_elt)[2], ((unsigned int*)sptr_elt)[2], u32pm, u32npm); \
						OP(((unsigned int*)dptr_elt)[3], ((unsigned int*)sptr_elt)[3], u32pm, u32npm); \
						dptr_elt += 16;									\
						sptr_elt += 16;									\
					}													\
				}														\
				for ( ; i < (wi&(~3)) ; i+= 4) {						\
					OP(((unsigned int*)dptr_elt)[0], ((unsigned int*)sptr_elt)[0], u32pm, u32npm); \
					dptr_elt += 4;										\
					sptr_elt += 4;										\
				}														\
			}															\
		}																\
		for ( ; i < wi ; i++) {											\
			OP(*dptr_elt, *sptr_elt, pm, npm);							\
			dptr_elt ++;												\
			sptr_elt ++;												\
		}																\
		sptr_line += HRES;												\
		dptr_line += HRES;												\
	}																	\
	}

#define BLIT_FWD_BWD(NAME, OP) \
	static void bitblit_fwd_bwd_##NAME(const unsigned_param_type xs,	\
									   const unsigned_param_type ys,	\
									   const unsigned_param_type wi,	\
									   const unsigned_param_type re,	\
									   const unsigned_param_type xd,	\
									   const unsigned_param_type yd,	\
									   const unsigned char pm) {		\
		unsigned int i, j;												\
		unsigned char *sptr = (((unsigned char *)BASE_FB) + mul_HRES(ys) + xs); \
		unsigned char *dptr = (((unsigned char *)BASE_FB) + mul_HRES(yd) + xd); \
		unsigned char *sptr_line = sptr + wi - 1;						\
		unsigned char *dptr_line = dptr + wi - 1;						\
		const unsigned char npm = ~pm;									\
																		\
		for (j = 0 ; j < re ; j++) {									\
			unsigned char *sptr_elt = sptr_line;						\
			unsigned char *dptr_elt = dptr_line;						\
			for (i = 0 ; i < wi ; i++) {								\
				OP(*dptr_elt, *sptr_elt, pm, npm);						\
				dptr_elt --;											\
				sptr_elt --;											\
			}															\
			sptr_line += HRES;											\
			dptr_line += HRES;											\
		}																\
	}

#define BLIT_BWD_FWD(NAME, OP)											\
	static void bitblit_bwd_fwd_##NAME(const unsigned_param_type xs,	\
									   const unsigned_param_type ys,	\
									   const unsigned_param_type wi,	\
									   const unsigned_param_type re,	\
									   const unsigned_param_type xd,	\
									   const unsigned_param_type yd,	\
									   const unsigned char pm) {		\
	unsigned int i, j;													\
	unsigned char *sptr = (((unsigned char *)BASE_FB) + mul_HRES(ys) + xs); \
	unsigned char *dptr = (((unsigned char *)BASE_FB) + mul_HRES(yd) + xd); \
	unsigned char *sptr_line = sptr + mul_HRES(re-1);					\
	unsigned char *dptr_line = dptr + mul_HRES(re-1);					\
	const unsigned char npm = ~pm;										\
																		\
	for (j = 0 ; j < re ; j++) {										\
		unsigned char *sptr_elt = sptr_line;							\
		unsigned char *dptr_elt = dptr_line;							\
		i = 0;															\
		if (wi>3) {														\
			if ((xs & 0x3) || (xd & 0x3)) {								\
				for ( ; i < wi && ((unsigned int)dptr_elt&0x3)!=0; i++) { \
					OP(*dptr_elt, *sptr_elt, pm, npm);					\
					dptr_elt ++;										\
					sptr_elt ++;										\
				}														\
				unsigned char *sptr_elt_al = (unsigned char*)((unsigned int)sptr_elt & ~0x3); \
				unsigned int fsr_cst = 8*((unsigned int)sptr_elt & 0x3); \
				unsigned int src0 = ((unsigned int*)sptr_elt_al)[0];	\
				unsigned int u32pm = (unsigned int)pm | ((unsigned int)pm)<<8 | ((unsigned int)pm)<<16 | ((unsigned int)pm)<<24; \
				for ( ; i < (wi-3) ; i+=4) {							\
					unsigned int src1 = ((unsigned int*)sptr_elt_al)[1]; \
					unsigned int val;									\
					asm("fsr %0, %1, %2, %3\n" : "=r"(val) : "r"(src0), "r"(src1), "r"(fsr_cst)); \
					OP(*(unsigned int*)dptr_elt, val, u32pm, u32npm);	\
					src0 = src1;										\
					dptr_elt += 4;										\
					sptr_elt_al += 4;									\
				}														\
				sptr_elt = sptr_elt_al + ((unsigned int)sptr_elt & 0x3); \
			} else {													\
				if (((xs & 0xf) == 0) && ((xd & 0xf) == 0)) {			\
					for ( ; i < (wi&(~0xf)) ; i+= 16) {					\
						const unsigned int u32pm = (unsigned int)pm | ((unsigned int)pm)<<8 | ((unsigned int)pm)<<16 | ((unsigned int)pm)<<24; \
						/*const unsigned int u32npm = (unsigned int)npm | ((unsigned int)npm)<<8 | ((unsigned int)npm)<<16 | ((unsigned int)npm)<<24;*/ \
						OP(((unsigned int*)dptr_elt)[0], ((unsigned int*)sptr_elt)[0], u32pm, u32npm); \
						OP(((unsigned int*)dptr_elt)[1], ((unsigned int*)sptr_elt)[1], u32pm, u32npm); \
						OP(((unsigned int*)dptr_elt)[2], ((unsigned int*)sptr_elt)[2], u32pm, u32npm); \
						OP(((unsigned int*)dptr_elt)[3], ((unsigned int*)sptr_elt)[3], u32pm, u32npm); \
						dptr_elt += 16;									\
						sptr_elt += 16;									\
					}													\
				}														\
				if (((xs & 0x3) == 0) && ((xd & 0x3) == 0)) {			\
					for ( ; i < (wi&(~3)) ; i+= 4) {					\
						const unsigned int u32pm = (unsigned int)pm | ((unsigned int)pm)<<8 | ((unsigned int)pm)<<16 | ((unsigned int)pm)<<24; \
						/*const unsigned int u32npm = (unsigned int)npm | ((unsigned int)npm)<<8 | ((unsigned int)npm)<<16 | ((unsigned int)npm)<<24;*/ \
						OP(((unsigned int*)dptr_elt)[0], ((unsigned int*)sptr_elt)[0], u32pm, u32npm); \
						dptr_elt += 4;									\
						sptr_elt += 4;									\
					}													\
				}														\
			}															\
		}																\
		for ( ; i < wi ; i++) {											\
			OP(*dptr_elt, *sptr_elt, pm, npm);							\
			dptr_elt ++;												\
			sptr_elt ++;												\
		}																\
		sptr_line -= HRES;												\
		dptr_line -= HRES;												\
	}																	\
	}


#define BLIT_ALLDIR(NAME, OP)				\
	BLIT_FWD_FWD(NAME, OP)					\
	BLIT_FWD_BWD(NAME, OP)					\
	BLIT_BWD_FWD(NAME, OP)					\
	

BLIT_ALLDIR(copy, COPY)
BLIT_ALLDIR(xor, XOR)
BLIT_ALLDIR(copy_pm, COPY_PM)
BLIT_ALLDIR(xor_pm, XOR_PM)

#if 0
		else if ((xd & 0xf) == 0) {
			unsigned int fsr_cst = xs & 0x3;
			unsigned char* sptr_elt_al = sptr_elt - fsr_cst;
			unsigned int src0 = ((unsigned int*)sptr_elt_al)[0];
			for ( ; i < (wi&(~0xf)) ; i+= 16) {
				unsigned int src1, val;

				src1 = ((unsigned int*)sptr_elt_al)[1];
				val = _rv32_fsr(src0, src1, fsr_cst);
				((unsigned int*)dptr_elt)[0] = val;
				src0 = src1;

				src1 = ((unsigned int*)sptr_elt_al)[2];
				val = _rv32_fsr(src0, src1, fsr_cst);
				((unsigned int*)dptr_elt)[1] = val;
				src0 = src1;

				src1 = ((unsigned int*)sptr_elt_al)[3];
				val = _rv32_fsr(src0, src1, fsr_cst);
				((unsigned int*)dptr_elt)[2] = val;
				src0 = src1;

				src1 = ((unsigned int*)sptr_elt_al)[4];
				val = _rv32_fsr(src0, src1, fsr_cst);
				((unsigned int*)dptr_elt)[3] = val;
				src0 = src1;
	
				dptr_elt += 16;
				sptr_elt_al += 16;
			}
      
		}
#endif

#if 0
static void bitblit_bwd_bwd_copy(const unsigned_param_type xs,
						  const unsigned_param_type ys,
						  const unsigned_param_type wi,
						  const unsigned_param_type re,
						  const unsigned_param_type xd,
						  const unsigned_param_type yd,
						  const unsigned char pm
						  ) {
	unsigned int i, j;
	unsigned char *sptr = (((unsigned char *)BASE_FB) + mul_HRES(ys) + xs);
	unsigned char *dptr = (((unsigned char *)BASE_FB) + mul_HRES(yd) + xd);
	unsigned char *sptr_line = sptr + mul_HRES(re-1);
	unsigned char *dptr_line = dptr + mul_HRES(re-1);

	// flush_cache(); // handled in boot()
  
	for (j = 0 ; j < re ; j++) {
		unsigned char *sptr_elt = sptr_line + wi - 1;
		unsigned char *dptr_elt = dptr_line + wi - 1;
		for (i = 0 ; i < wi ; i++) {
			*dptr_elt = *sptr_elt;
			dptr_elt --;
			sptr_elt --;
		}
		sptr_line -= HRES;
		dptr_line -= HRES;
	}
}
#endif

#ifdef TRACE_ON_SCREEN
#include "blit_font.h"

static void print_hex(unsigned char v, unsigned char* line_fb);
static void print_hex(unsigned char v, unsigned char* line_fb) {
	unsigned int x, y;
	const unsigned char *pbits = font + v * 8;
	for (y = 0 ; y < 8 ; y++) { // line in char
		const unsigned char bits = pbits[y];
		for (x = 0 ; x < 8 ; x++) { // bits in line
			unsigned char data = - ((bits>>(7-x))&1); // 0xff or 0x00
			line_fb[x] = data;
		}
		line_fb += HRES;
	}
}

static void print_hexword(unsigned int v, unsigned int bx, unsigned int by) {
	unsigned int i, j;
#if 0
	unsigned int x, y;
#endif
	unsigned char* base_fb = (((unsigned char *)BASE_FB) + mul_HRES(by) + bx);

	for (i = 0 ; i < 8 ; i++) { // nibbles in v
		unsigned char* line_fb = base_fb;
		unsigned int bidx = (v >> (28-i*4) & 0xF);
#if 0
		const unsigned char *pbits = font + bidx * 8;
		for (y = 0 ; y < 8 ; y++) { // line in char
			const unsigned char bits = pbits[y];
			for (x = 0 ; x < 8 ; x++) { // bits in line
				unsigned char data = - ((bits>>(7-x))&1); // 0xff or 0x00
				line_fb[x] = data;
			}
			line_fb += HRES;
		}
#else
		print_hex(bidx, line_fb);
#endif
		base_fb += 8;
	}
}

static void show_status_on_screen(void) {
	struct cg6_fbc* fbc = (struct cg6_fbc*)BASE_FBC;
	unsigned int cmd = fbc->fbc_r5_cmd;
	unsigned int alu = fbc->fbc_alu;
	unsigned int mode = fbc->fbc_mode;
	unsigned int bx = 0;
	unsigned int by = 640 + ((cmd & 0xF)*32);
	unsigned char* base_fb = (((unsigned char *)BASE_FB) + mul_HRES(by) + bx);

	print_hex(cmd & 0xF, base_fb);
	bx += 16;
	print_hexword(alu, bx, by);
	bx += 72;
	print_hexword(mode, bx, by);
	bx -= 72;
	by +=  8;
	if ((cmd & 0xF) == FUN_DRAW) {
		print_hexword(fbc->fbc_arectx_prev, bx, by);
		bx += 72;
		print_hexword(fbc->fbc_arecty_prev, bx, by);
		bx -= 72;
		by +=  8;
		print_hexword(fbc->fbc_arectx, bx, by);
		bx += 72;
		print_hexword(fbc->fbc_arecty, bx, by);
		bx -= 72;
		by +=  8;
		print_hexword(fbc->fbc_pm, bx, by);
		bx -= 88;
	} else if ((cmd &  0xF) == FUN_BLIT) {
		print_hexword(fbc->fbc_x0, bx, by);
		bx += 72;
		print_hexword(fbc->fbc_y0, bx, by);
		bx += 72;
		print_hexword(fbc->fbc_x1, bx, by);
		bx += 72;
		print_hexword(fbc->fbc_y1, bx, by);
		bx -= 216;
		by +=  8;
		print_hexword(fbc->fbc_x2, bx, by);
		bx += 72;
		print_hexword(fbc->fbc_y2, bx, by);
		bx += 72;
		print_hexword(fbc->fbc_x3, bx, by);
		bx += 72;
		print_hexword(fbc->fbc_y3, bx, by);
		bx -= 216;
		by +=  8;
		print_hexword(fbc->fbc_pm, bx, by);
		bx -= 88;
	}
	print_hexword(fbc->fbc_s, bx, by);
}
#endif
