MelkhiorVintageComputing/SBusFPGA/sbus-to-ztex-gateware-migen/neorv32_trng_patched.vhd

-- # THIS IS NOT THE ORIGINAL FILE
-- # THIS WAS MODIFIED TO EXPOSE THE TRNG IN LITEX
-- # See the link in the copyright header to find the original file
--
--
-- #################################################################################################
-- # << NEORV32 - True Random Number Generator (TRNG) >>                                           #
-- # ********************************************************************************************* #
-- # This unit implements a *true* random number generator which uses several ring oscillators as  #
-- # entropy source. The outputs of all chains are XORed and de-biased using a John von Neumann    #
-- # randomness extractor. The de-biased signal is further processed by a simple LFSR for improved #
-- # whitening.                                                                                    #
-- # ********************************************************************************************* #
-- # BSD 3-Clause License                                                                          #
-- #                                                                                               #
-- # Copyright (c) 2021, Stephan Nolting. All rights reserved.                                     #
-- #                                                                                               #
-- # Redistribution and use in source and binary forms, with or without modification, are          #
-- # permitted provided that the following conditions are met:                                     #
-- #                                                                                               #
-- # 1. Redistributions of source code must retain the above copyright notice, this list of        #
-- #    conditions and the following disclaimer.                                                   #
-- #                                                                                               #
-- # 2. Redistributions in binary form must reproduce the above copyright notice, this list of     #
-- #    conditions and the following disclaimer in the documentation and/or other materials        #
-- #    provided with the distribution.                                                            #
-- #                                                                                               #
-- # 3. Neither the name of the copyright holder nor the names of its contributors may be used to  #
-- #    endorse or promote products derived from this software without specific prior written      #
-- #    permission.                                                                                #
-- #                                                                                               #
-- # THIS SOFTWARE IS PROVIDED BY THE COPYRIGHT HOLDERS AND CONTRIBUTORS "AS IS" AND ANY EXPRESS   #
-- # OR IMPLIED WARRANTIES, INCLUDING, BUT NOT LIMITED TO, THE IMPLIED WARRANTIES OF               #
-- # MERCHANTABILITY AND FITNESS FOR A PARTICULAR PURPOSE ARE DISCLAIMED. IN NO EVENT SHALL THE    #
-- # COPYRIGHT HOLDER OR CONTRIBUTORS BE LIABLE FOR ANY DIRECT, INDIRECT, INCIDENTAL, SPECIAL,     #
-- # EXEMPLARY, OR CONSEQUENTIAL DAMAGES (INCLUDING, BUT NOT LIMITED TO, PROCUREMENT OF SUBSTITUTE #
-- # GOODS OR SERVICES; LOSS OF USE, DATA, OR PROFITS; OR BUSINESS INTERRUPTION) HOWEVER CAUSED    #
-- # AND ON ANY THEORY OF LIABILITY, WHETHER IN CONTRACT, STRICT LIABILITY, OR TORT (INCLUDING     #
-- # NEGLIGENCE OR OTHERWISE) ARISING IN ANY WAY OUT OF THE USE OF THIS SOFTWARE, EVEN IF ADVISED  #
-- # OF THE POSSIBILITY OF SUCH DAMAGE.                                                            #
-- # ********************************************************************************************* #
-- # The NEORV32 Processor - https://github.com/stnolting/neorv32              (c) Stephan Nolting #
-- #################################################################################################

library ieee;
use ieee.std_logic_1164.all;
use ieee.numeric_std.all;

library neorv32;
-- use neorv32.neorv32_package.all;

entity neorv32_trng is
  port (
    -- host access --
    clk_i  : in  std_ulogic; -- global clock line
--    addr_i : in  std_ulogic_vector(31 downto 0); -- address
    rden_i : in  std_ulogic; -- read enable
    wren_i : in  std_ulogic; -- write enable
    data_i : in  std_ulogic_vector(31 downto 0); -- data in
    data_o : out std_ulogic_vector(31 downto 0)--; -- data out
--    ack_o  : out std_ulogic  -- transfer acknowledge
  );
end neorv32_trng;

architecture neorv32_trng_rtl of neorv32_trng is

  -- Advanced Configuration --------------------------------------------------------------------------------
  constant num_roscs_c     : natural := 4; -- total number of ring oscillators
  constant num_inv_start_c : natural := 5; -- number of inverters in FIRST ring oscillator (has to be odd)
  constant num_inv_inc_c   : natural := 2; -- number of inverters increment for each next ring oscillator (has to be even)
  constant lfsr_en_c       : boolean := true; -- use LFSR-based post-processing
  constant lfsr_taps_c     : std_ulogic_vector(7 downto 0) := "10111000"; -- Fibonacci post-processing LFSR feedback taps
  -- -------------------------------------------------------------------------------------------------------

  -- control register bits --
  constant ctrl_data_lsb_c : natural :=  0; -- r/-: Random data byte LSB
  constant ctrl_data_msb_c : natural :=  7; -- r/-: Random data byte MSB
  --
  constant ctrl_en_c       : natural := 30; -- r/w: TRNG enable
  constant ctrl_valid_c    : natural := 31; -- r/-: Output data valid

  -- IO space: module base address --
--  constant hi_abb_c : natural := index_size_f(io_size_c)-1; -- high address boundary bit
--  constant lo_abb_c : natural := index_size_f(trng_size_c); -- low address boundary bit

-- copy/pasted from the rtl/core/neorv32_package.vhd file
  function xor_reduce_f(a : std_ulogic_vector) return std_ulogic is
    variable tmp_v : std_ulogic;
  begin
    tmp_v := '0';
    if (a'low < a'high) then -- not null range?
      for i in a'low to a'high loop
        tmp_v := tmp_v xor a(i);
      end loop; -- i
    end if;
    return tmp_v;
  end function xor_reduce_f;


  -- Component: Ring-Oscillator --
  component neorv32_trng_ring_osc
    generic (
      NUM_INV : natural := 16 -- number of inverters in chain
    );
    port (
      clk_i    : in  std_ulogic;
      enable_i : in  std_ulogic; -- enable chain input
      enable_o : out std_ulogic; -- enable chain output
      data_o   : out std_ulogic  -- sync random bit
    );
  end component;

  -- access control --
  signal acc_en : std_ulogic; -- module access enable
--  signal wren   : std_ulogic; -- full word write enable
--  signal rden   : std_ulogic; -- read enable

  -- ring-oscillator array --
  signal osc_array_en_in  : std_ulogic_vector(num_roscs_c-1 downto 0);
  signal osc_array_en_out : std_ulogic_vector(num_roscs_c-1 downto 0);
  signal osc_array_data   : std_ulogic_vector(num_roscs_c-1 downto 0);

  -- von-Neumann de-biasing --
  type debiasing_t is record
    sreg  : std_ulogic_vector(1 downto 0);
    state : std_ulogic; -- process de-biasing every second cycle
    valid : std_ulogic; -- de-biased data
    data  : std_ulogic; -- de-biased data valid
  end record;
  signal debiasing : debiasing_t;

  -- (post-)processing core --
  type processing_t is record
    enable : std_ulogic; -- TRNG enable flag
    cnt    : std_ulogic_vector(3 downto 0); -- bit counter
    sreg   : std_ulogic_vector(7 downto 0); -- data shift register
    output : std_ulogic_vector(7 downto 0); -- output register
    valid  : std_ulogic; -- data output valid flag
  end record;
  signal processing : processing_t;
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
